MugenMicko/voron/V0/5015_Toolhead/images/back.png

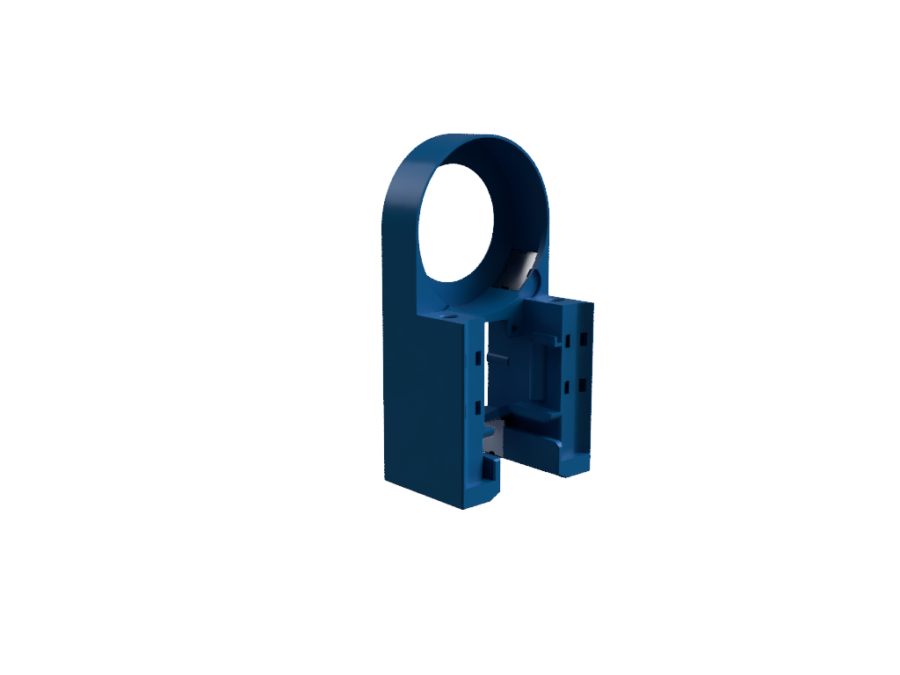
V0/5015_Toolhead/images/back.png
