MugenMicko/voron/V0/5015_Toolhead/images/front.png

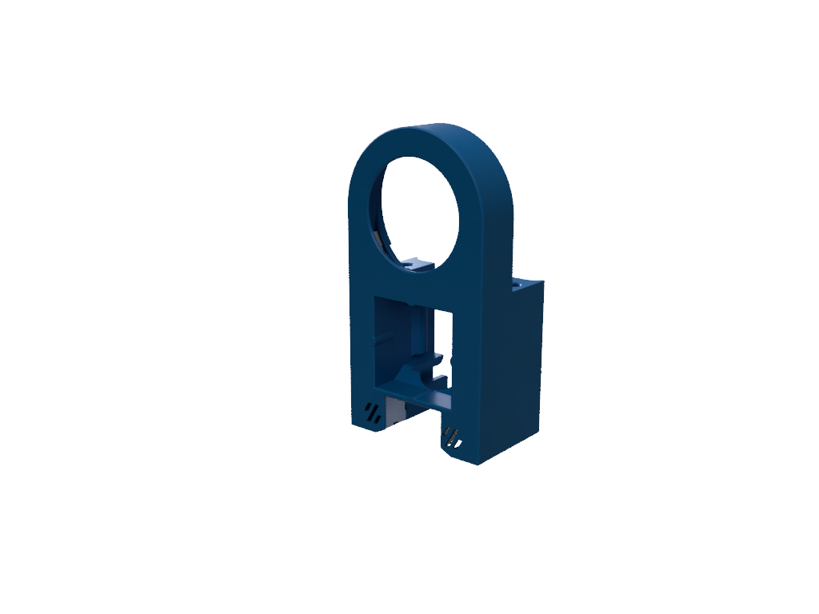
V0/5015_Toolhead/images/front.png
