MugenMicko/voron/V0/5015_Toolhead/images/ledsupports.png

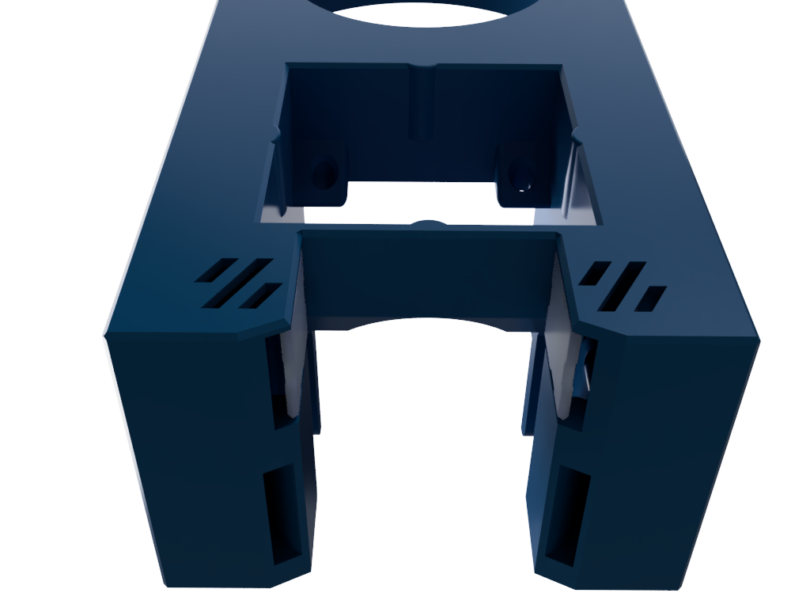
V0/5015_Toolhead/images/ledsupports.png
