MugenMicko/voron/V0/5015_Toolhead/images/PocketWatch2.jpg

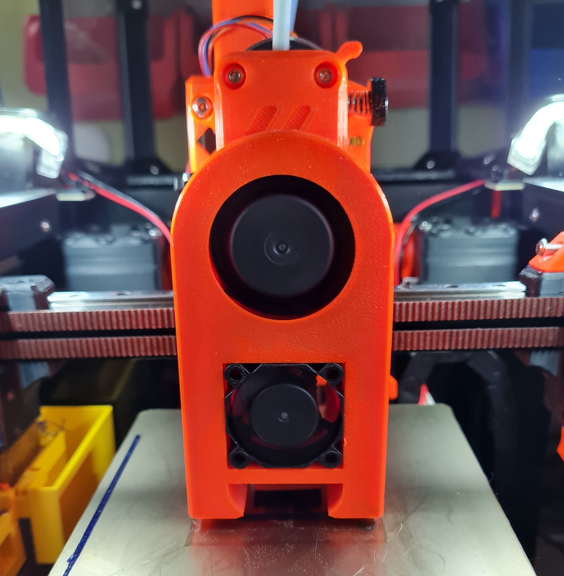
V0/5015_Toolhead/images/PocketWatch2.jpg
