MugenMicko/voron/V0/Dragon_Burner/images/airflow_db2.png

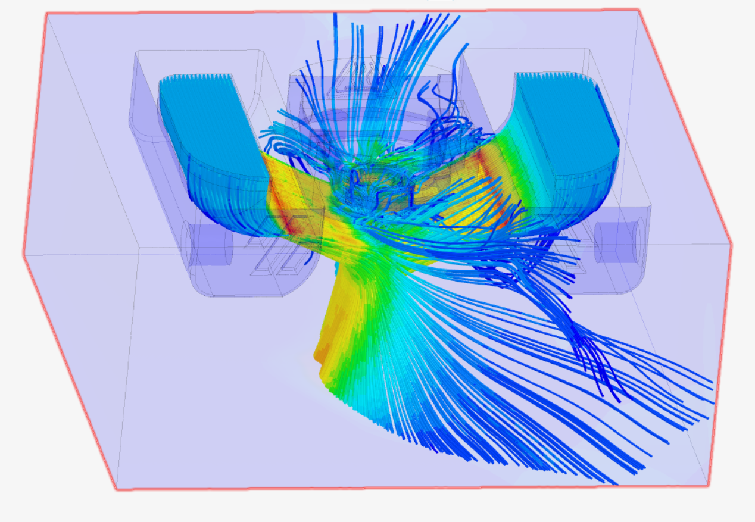
V0/Dragon_Burner/images/airflow_db2.png
