MugenMicko/voron/V0/Dragon_Burner/images/airflow_db.png

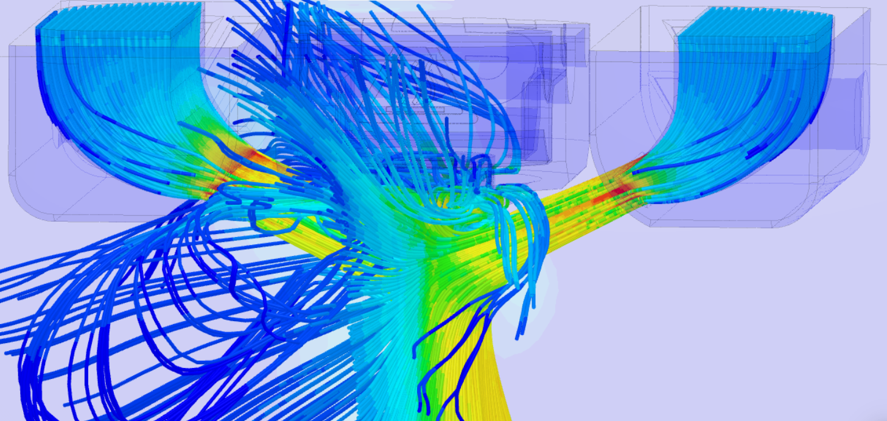
V0/Dragon_Burner/images/airflow_db.png
