MugenMicko/voron/V0/Dragon_Burner/images/airflowdb3.png

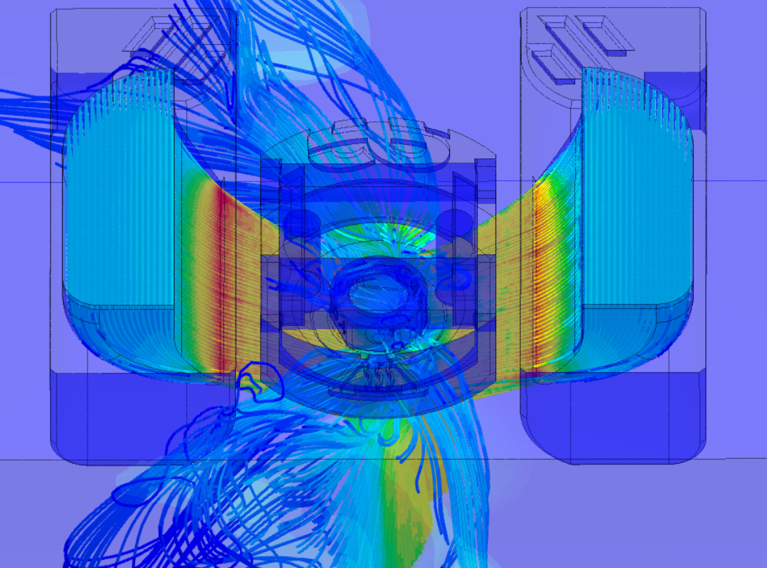
V0/Dragon_Burner/images/airflowdb3.png
