MugenMicko/voron/V0/NozzleWiper/images/mounted.jpg

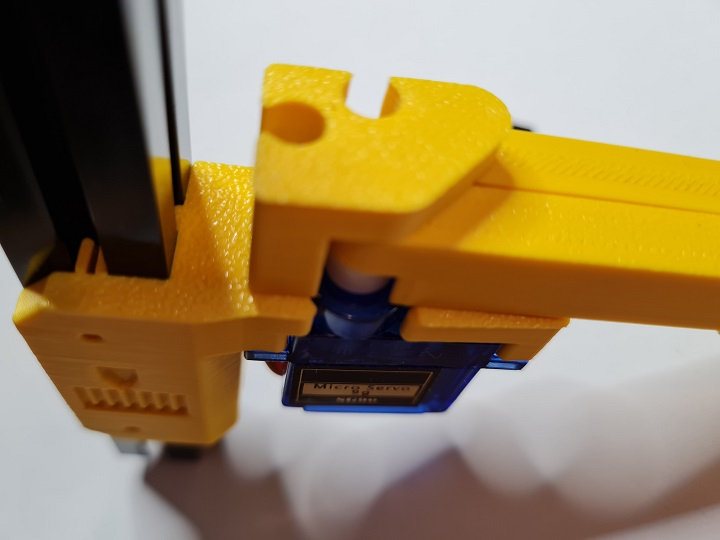
V0/NozzleWiper/images/mounted.jpg
