MugenMicko/voron/V0/NozzleWiper/images/wireplacement.jpg

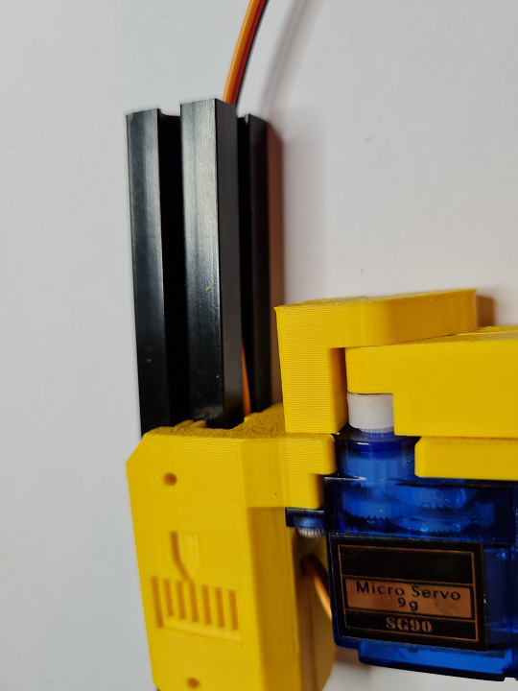
V0/NozzleWiper/images/wireplacement.jpg
