MugenMicko/voron/V0/Rapid_Burner/images/hf.png

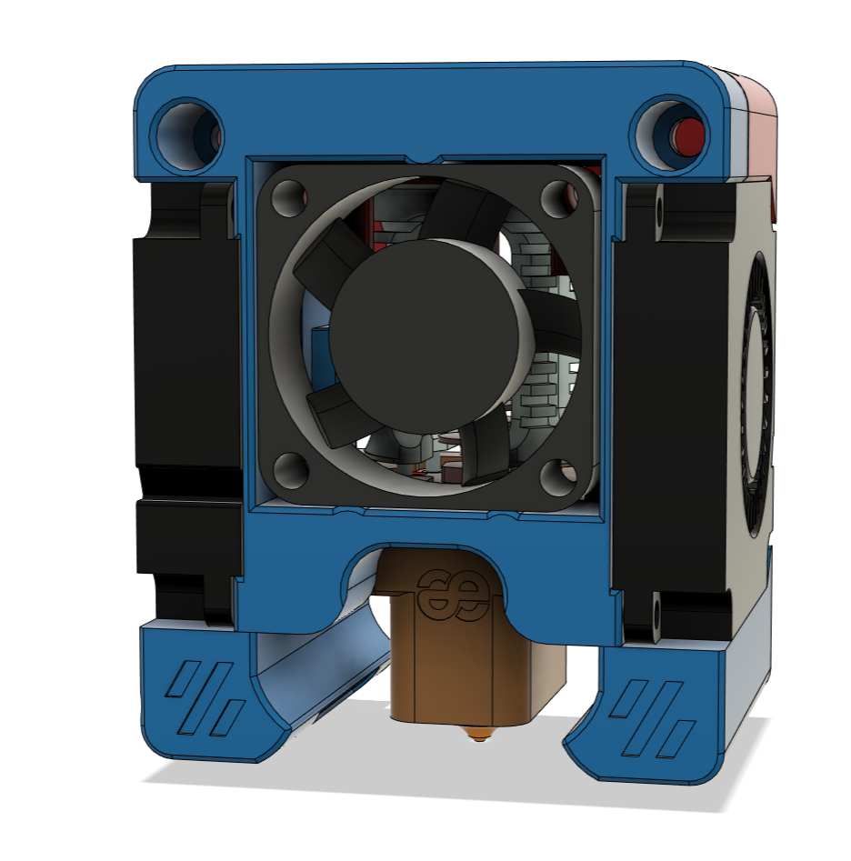
V0/Rapid_Burner/images/hf.png
