MugenMicko/voron/V0/TipTophat/images/toppanel.jpg

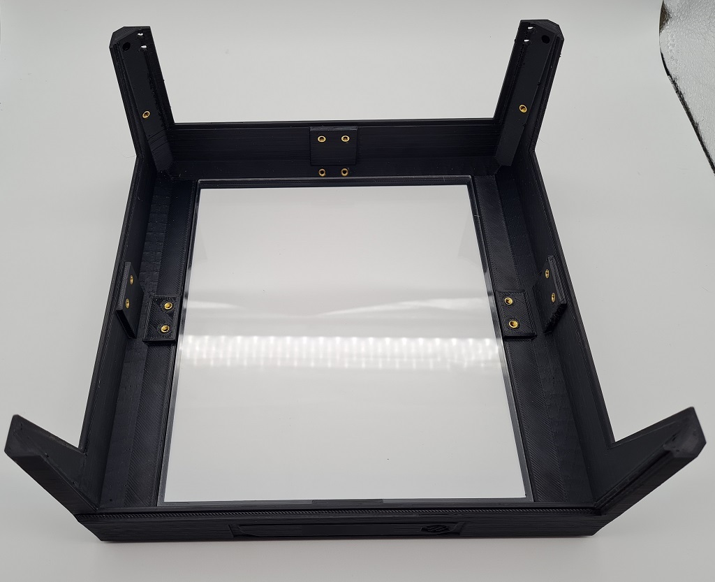
V0/TipTophat/images/toppanel.jpg
