MugenMicko/voron/general/RoundAbout/STLs/Latch.stl

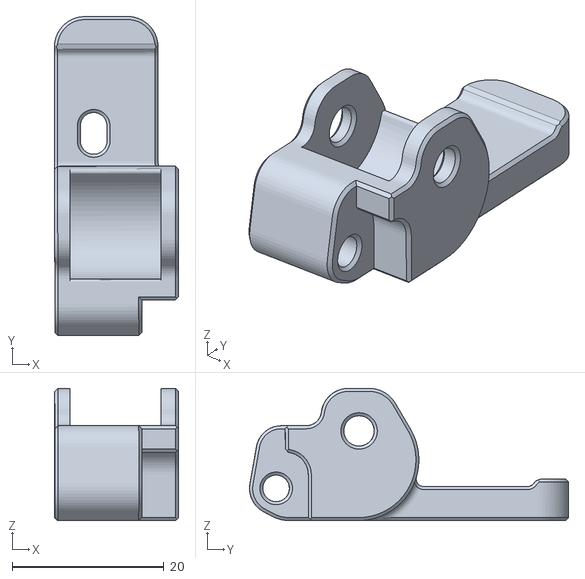
[picture p148: CAD file, 2022-09-11]
general/RoundAbout/STLs/Latch.stl
16.4 x 42.0 x 17.4
