MugenMicko/voron/general/RunoutUnklicky/STLs/Roller.stl

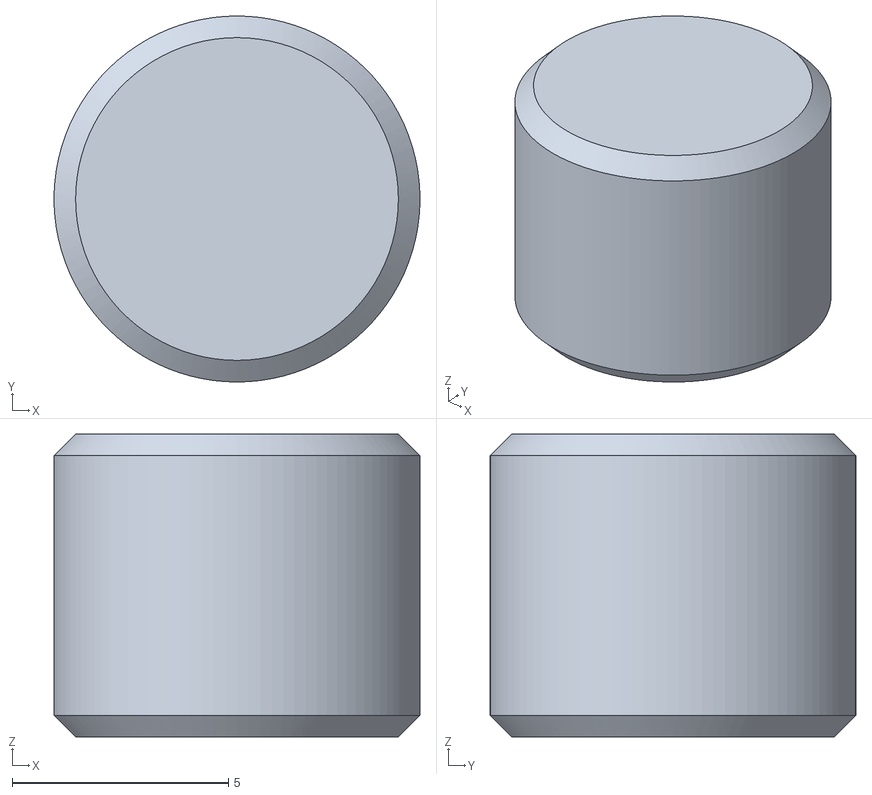
[picture p149: CAD file, 2022-07-18]
general/RunoutUnklicky/STLs/Roller.stl
8.46 x 8.46 x 7.00
