MugenMicko/voron/V0/5015_Toolhead/STLs/Bowden_Mount.stl

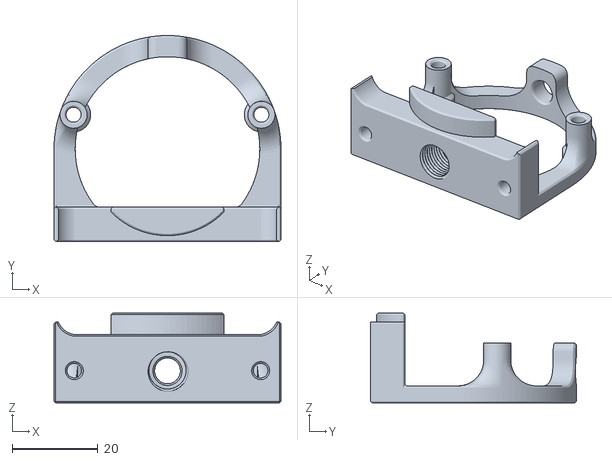
[picture p150: CAD file, 2022-09-22]
V0/5015_Toolhead/STLs/Bowden_Mount.stl
53.0 x 48.1 x 21.0
