MugenMicko/voron/V0/Dragon_Burner/STLs/Cowl_SlideSwipe.stl

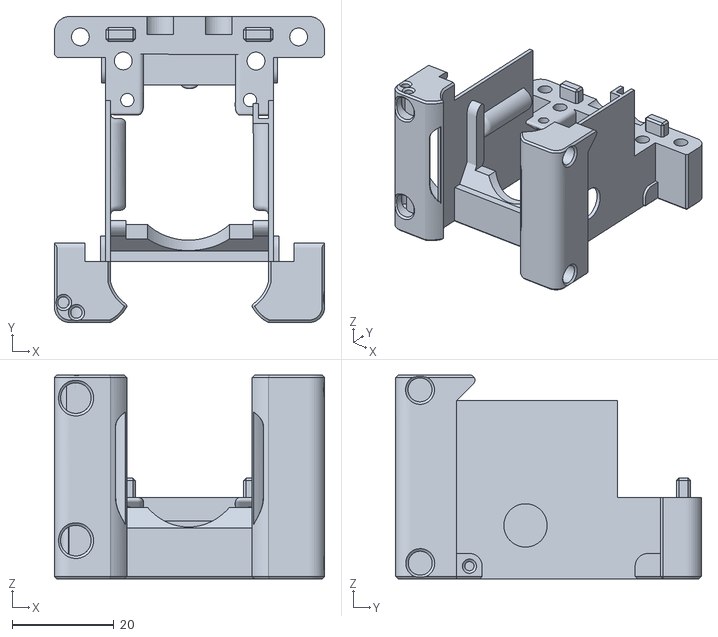
[picture p151: CAD file, 2022-09-30]
V0/Dragon_Burner/STLs/Cowl_SlideSwipe.stl
53.0 x 60.0 x 40.0
