MugenMicko/voron/V0/Dragon_Burner/STLs/Orbiter2/Dragon_Mount.stl

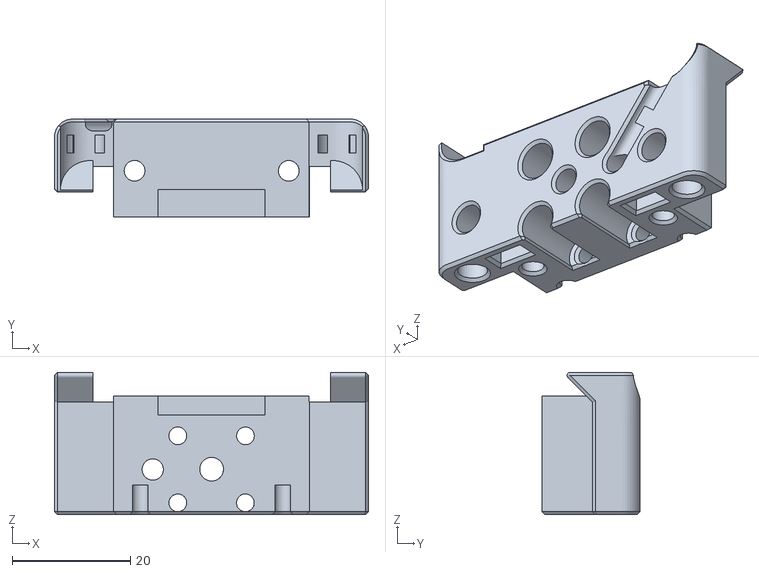
[picture p152: CAD file, 2022-08-28]
V0/Dragon_Burner/STLs/Orbiter2/Dragon_Mount.stl
53.0 x 16.5 x 24.0
