MugenMicko/voron/V0/NozzleWiper/STLs/Bucket.stl

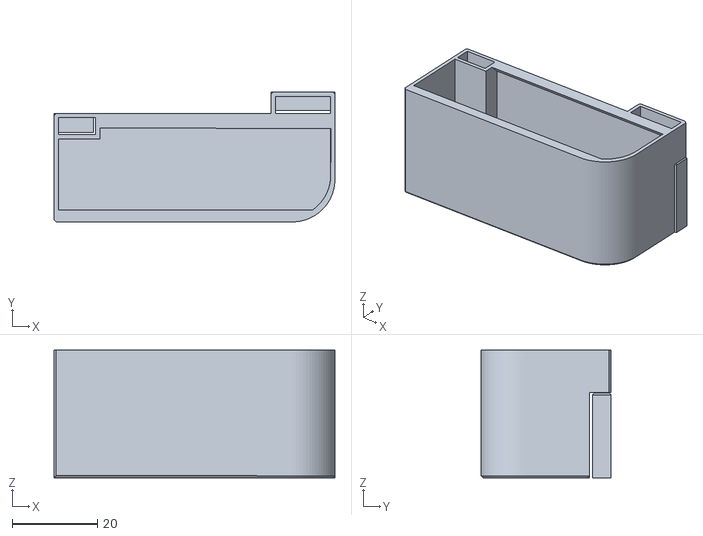
[picture p153: CAD file, 2022-09-01]
V0/NozzleWiper/STLs/Bucket.stl
66.0 x 30.5 x 30.0
