MugenMicko/voron/V0/Rapid_Burner/STLs/HF/Cowl_SlideSwipe.stl

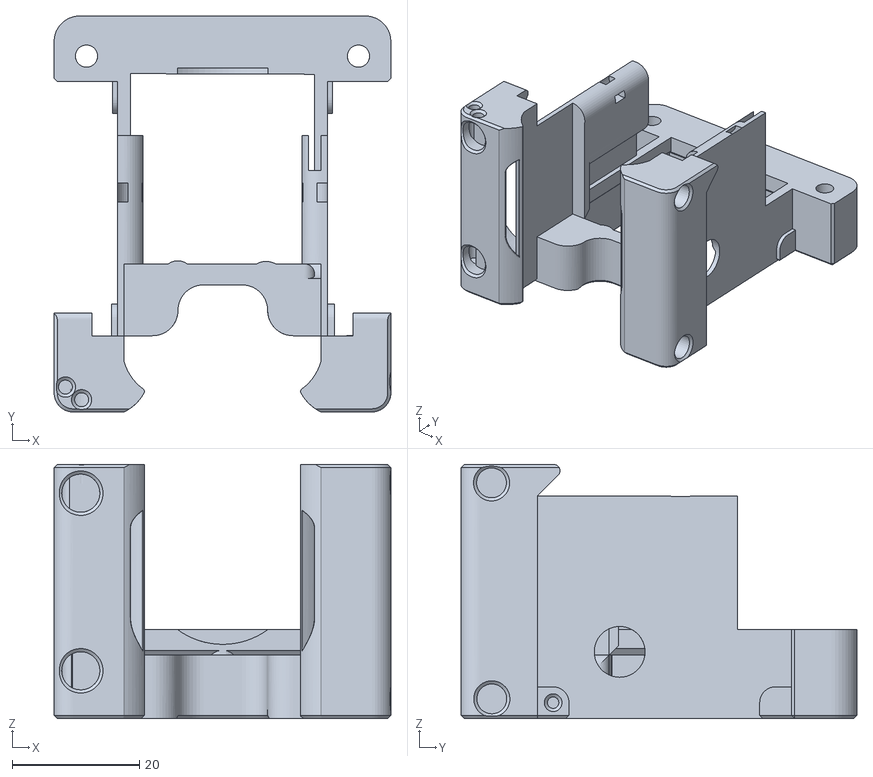
[picture p154: CAD file, 2022-09-06]
V0/Rapid_Burner/STLs/HF/Cowl_SlideSwipe.stl
53.0 x 62.3 x 40.0
