MugenMicko/voron/V0/Rapid_Burner/STLs/ZeroClick_Mount.stl

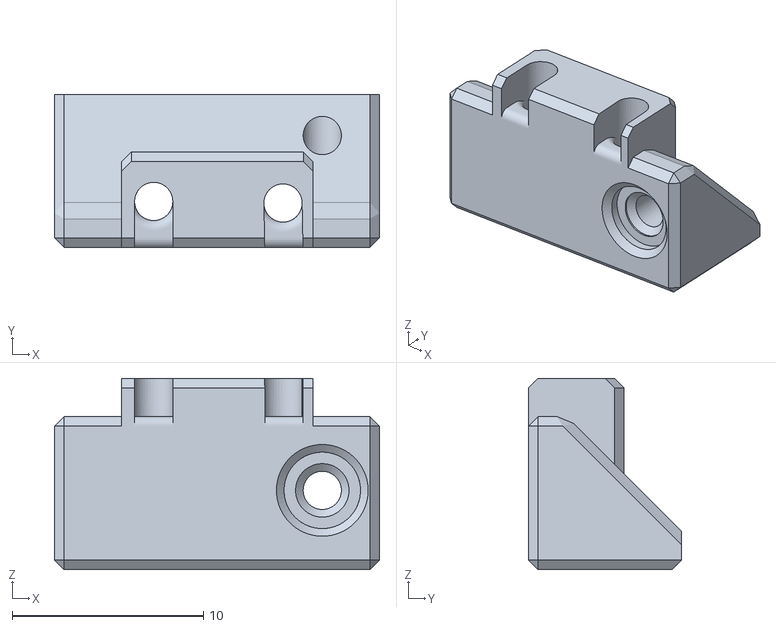
[picture p155: CAD file, 2022-09-21]
V0/Rapid_Burner/STLs/ZeroClick_Mount.stl
17.0 x 8.00 x 10.0
