MugenMicko/voron/V0/TipTophat/STLs/Peg_2_x2.stl

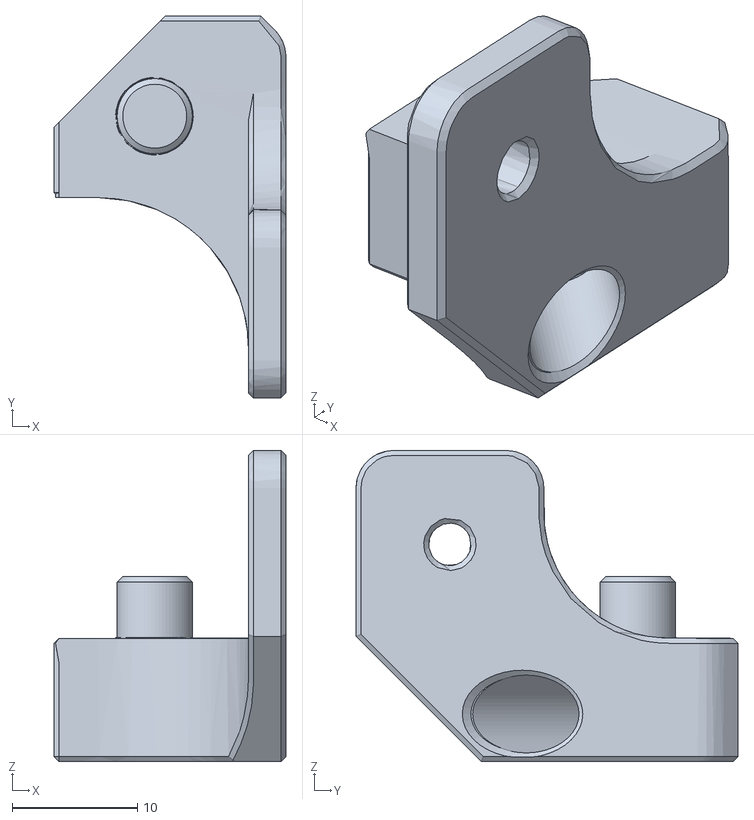
[picture p156: CAD file, 2022-07-24]
V0/TipTophat/STLs/Peg_2_x2.stl
18.5 x 30.5 x 24.8
