MugenMicko/voron/general/MiniMouse/STLs/MiniMouse_Guidler.stl

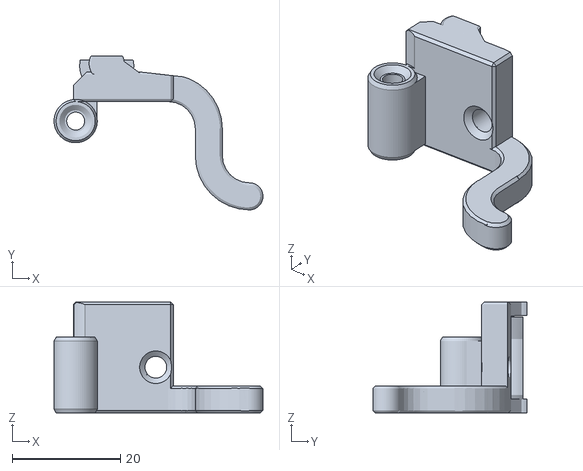
[picture p157: CAD file, 2022-06-26]
general/MiniMouse/STLs/MiniMouse_Guidler.stl
38.6 x 28.4 x 20.5
