MugenMicko/voron/general/RoundAbout/STLs/Support_Ring.stl

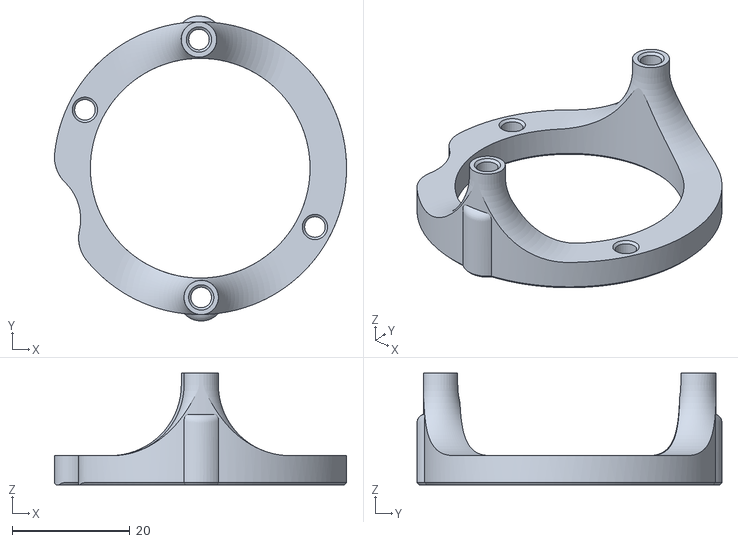
[picture p158: CAD file, 2022-09-11]
general/RoundAbout/STLs/Support_Ring.stl
49.6 x 51.8 x 19.0
