MugenMicko/voron/general/RoundHouse/STLs/Guidler.stl

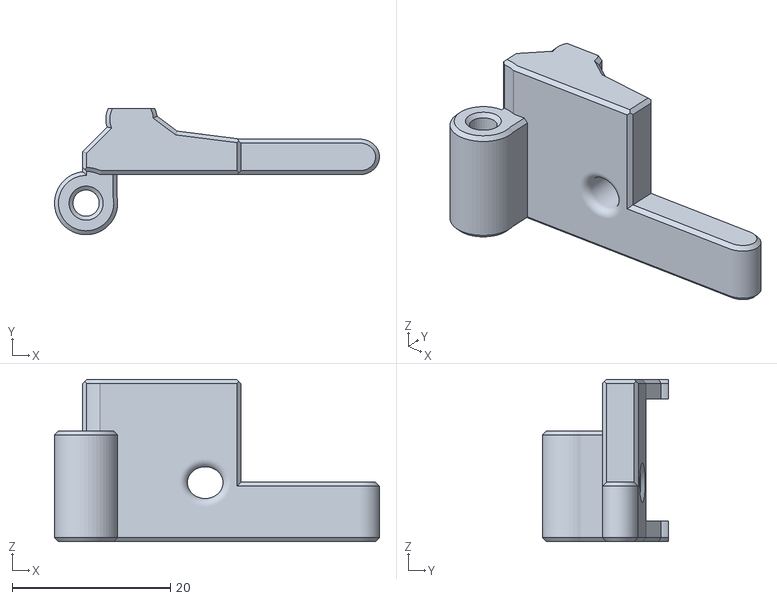
[picture p159: CAD file, 2022-08-05]
general/RoundHouse/STLs/Guidler.stl
41.1 x 16.0 x 20.5
