MugenMicko/voron/general/RunoutUnklicky/STLs/Top_2020.stl

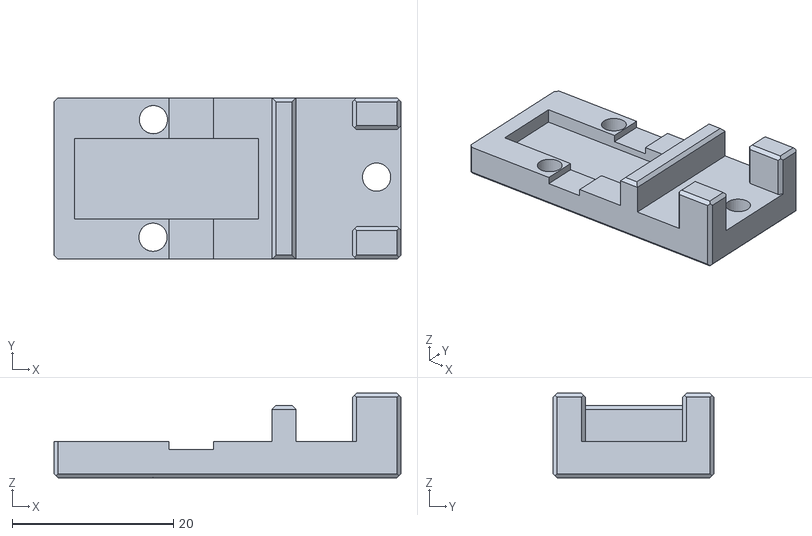
[picture p160: CAD file, 2022-07-15]
general/RunoutUnklicky/STLs/Top_2020.stl
43.0 x 20.0 x 10.5
