MugenMicko/voron/V0/5015_Toolhead/STLs/Fan_Cover.stl

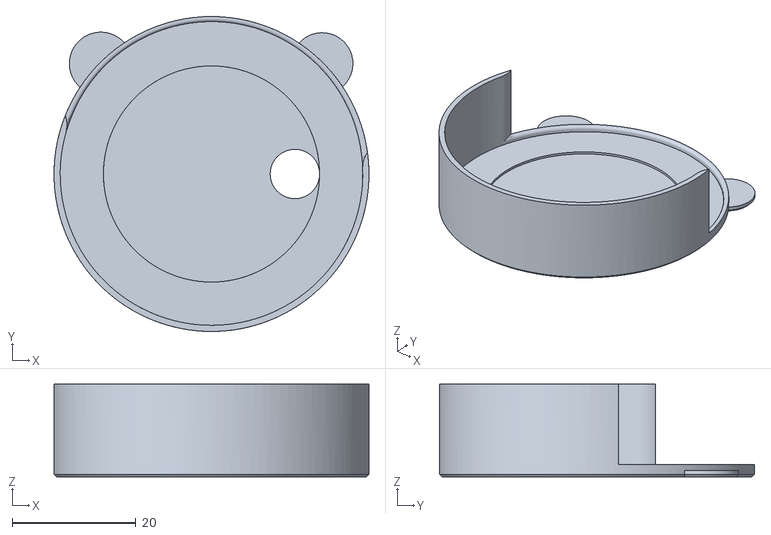
[picture p161: CAD file, 2022-09-12]
V0/5015_Toolhead/STLs/Fan_Cover.stl
51.0 x 51.0 x 15.0
