MugenMicko/voron/V0/Dragon_Burner/STLs/Orbiter1.5/Orbiter1.5_Mount.stl

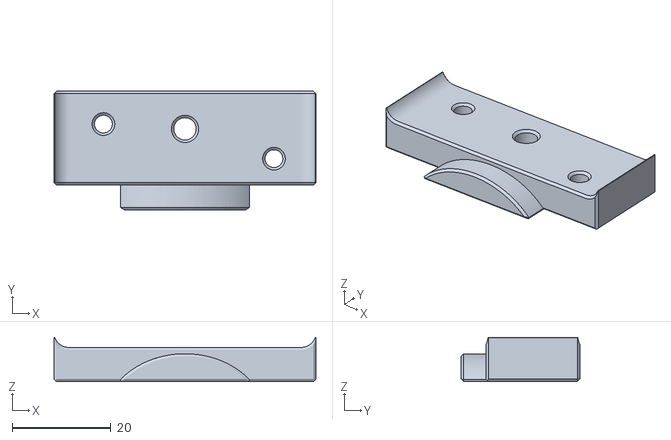
[picture p162: CAD file, 2022-08-29]
V0/Dragon_Burner/STLs/Orbiter1.5/Orbiter1.5_Mount.stl
53.0 x 24.1 x 8.90
