MugenMicko/voron/V0/NozzleWiper/STLs/Frame_Mount.stl

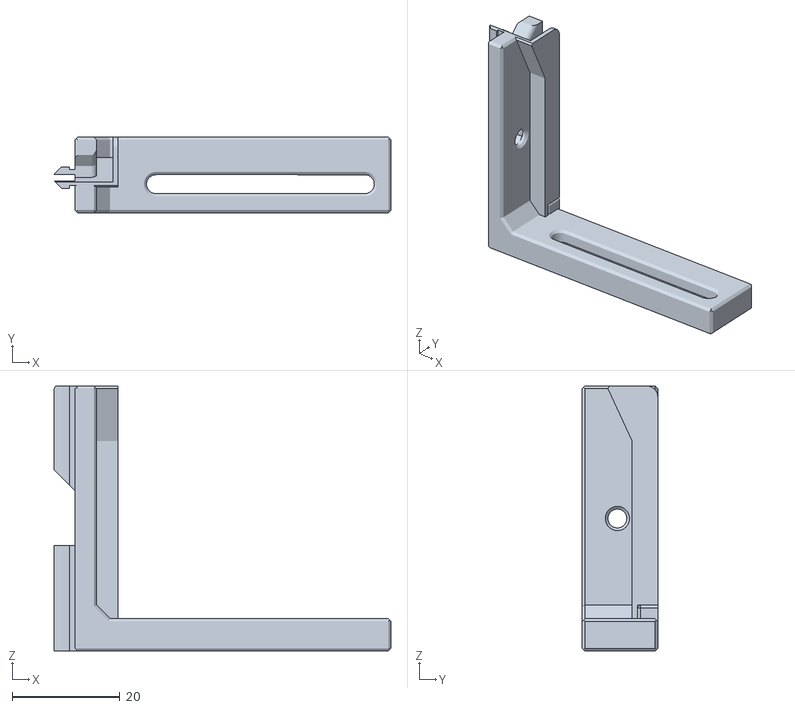
[picture p164: CAD file, 2022-08-21]
V0/NozzleWiper/STLs/Frame_Mount.stl
62.4 x 14.0 x 49.1
