MugenMicko/voron/V0/Rapid_Burner/STLs/Cowl_ZeroClick.stl

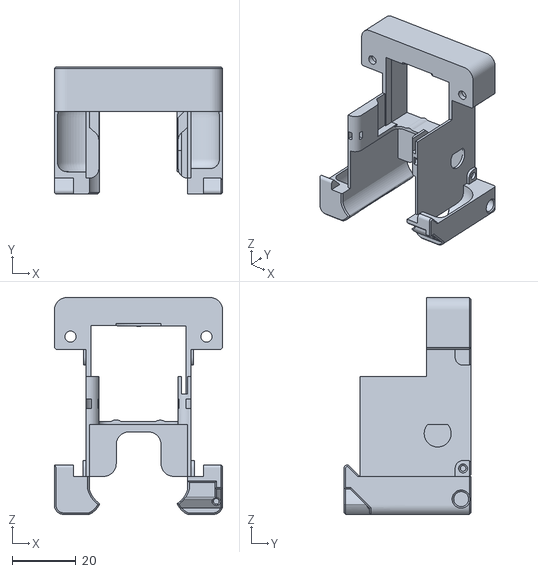
[picture p165: CAD file, 2022-09-21]
V0/Rapid_Burner/STLs/Cowl_ZeroClick.stl
53.0 x 40.0 x 68.3
