MugenMicko/voron/V0/TipTophat/STLs/Body_Q3.stl

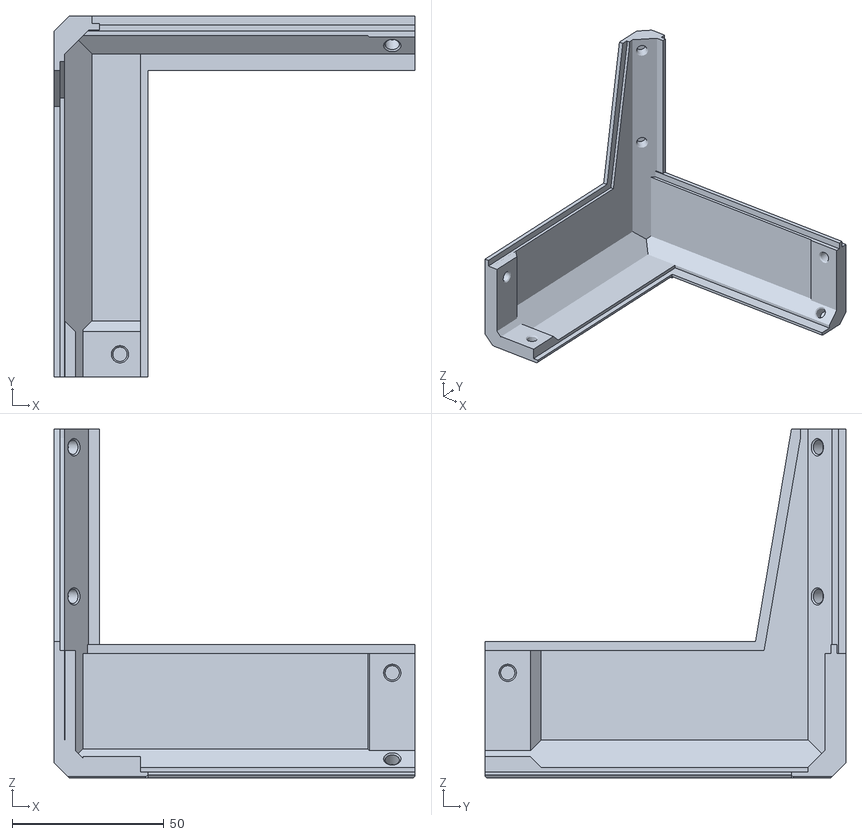
[picture p166: CAD file, 2022-07-12]
V0/TipTophat/STLs/Body_Q3.stl
119.0 x 119.0 x 115.0
