MugenMicko/voron/general/RoundAbout/STLs/Back.stl

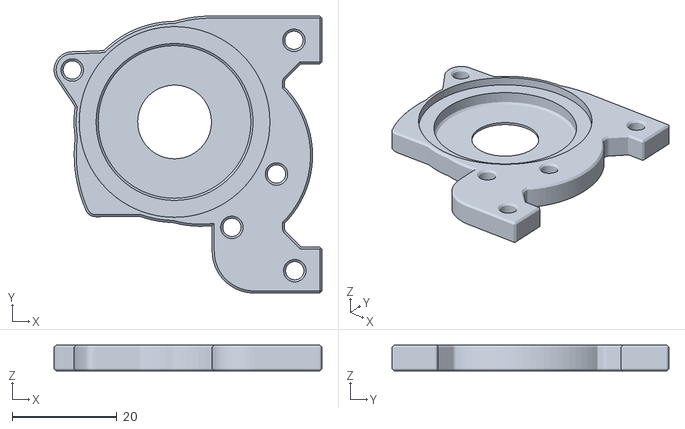
[picture p167: CAD file, 2022-09-11]
general/RoundAbout/STLs/Back.stl
51.2 x 53.0 x 4.95
