MugenMicko/voron/general/RunoutUnklicky/STLs/Top.stl

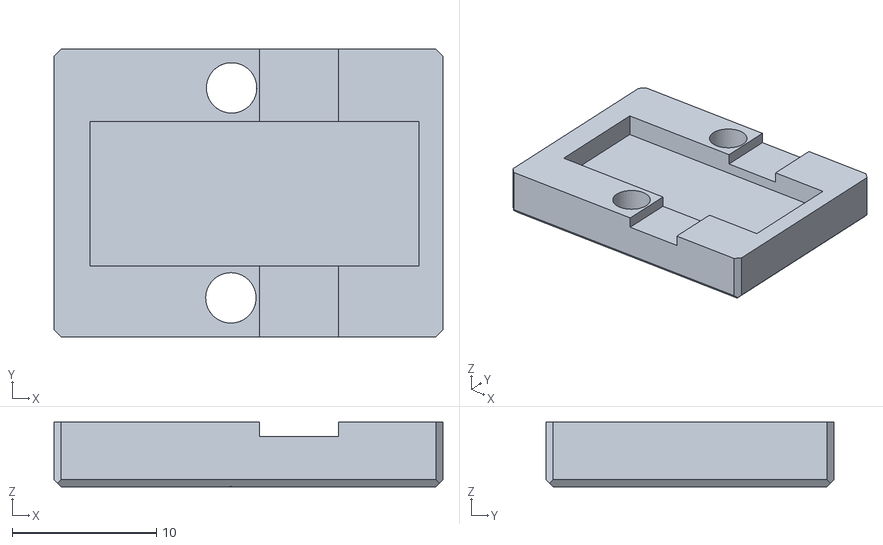
[picture p168: CAD file, 2022-07-15]
general/RunoutUnklicky/STLs/Top.stl
27.0 x 20.0 x 4.50
