MugenMicko/voron/V0/5015_Toolhead/STLs/Extruder_Mount.stl

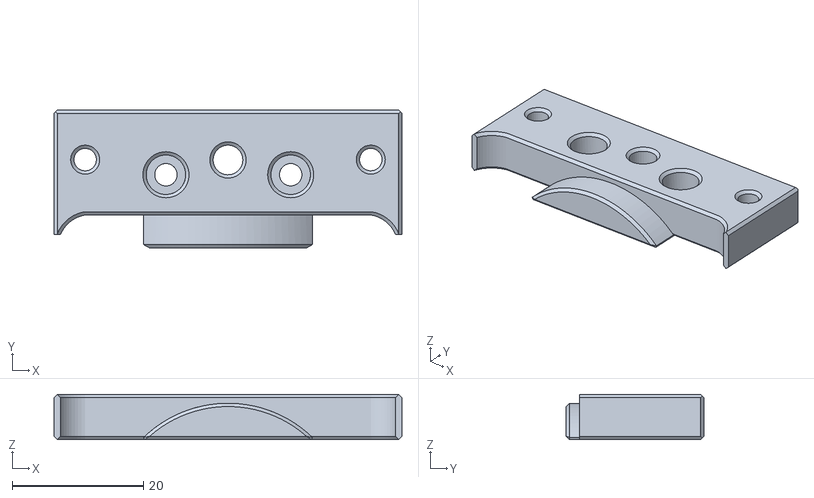
[picture p169: CAD file, 2022-08-30]
V0/5015_Toolhead/STLs/Extruder_Mount.stl
53.0 x 21.0 x 6.90
