MugenMicko/voron/V0/Dragon_Burner/STLs/Orbiter2/RapidoHF_Mount.stl

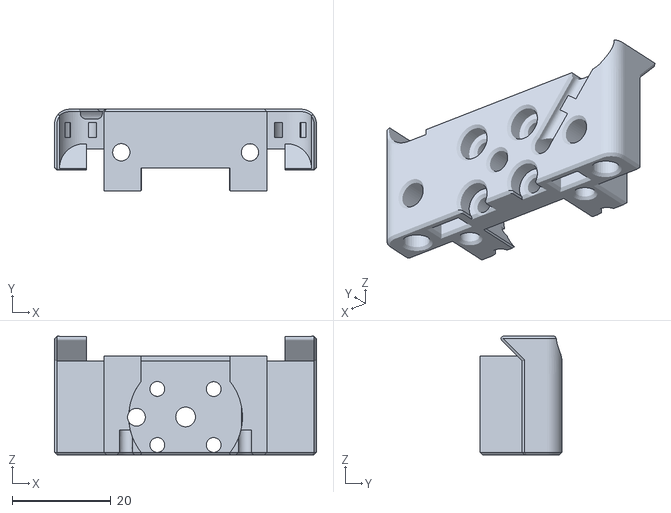
[picture p171: CAD file, 2022-08-28]
V0/Dragon_Burner/STLs/Orbiter2/RapidoHF_Mount.stl
53.0 x 16.5 x 24.0
