MugenMicko/voron/V0/NozzleWiper/STLs/Servo_Joint.stl

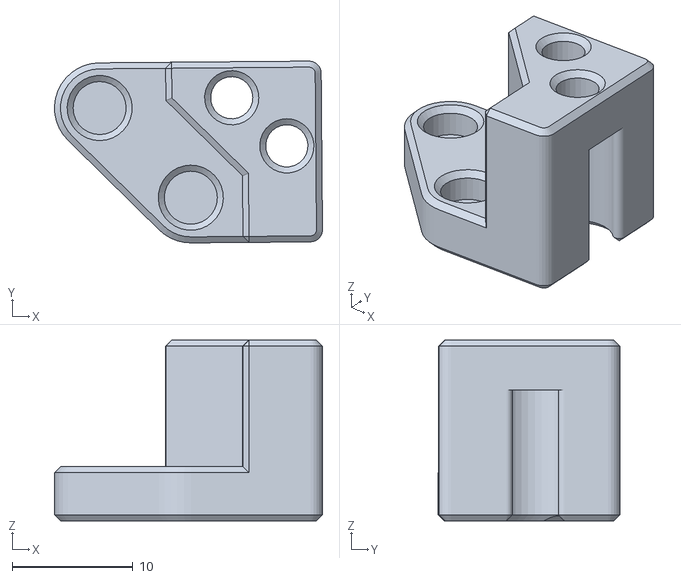
[picture p172: CAD file, 2022-08-21]
V0/NozzleWiper/STLs/Servo_Joint.stl
22.2 x 15.1 x 15.0
