MugenMicko/voron/V0/TipTophat/STLs/Body_Q4.stl

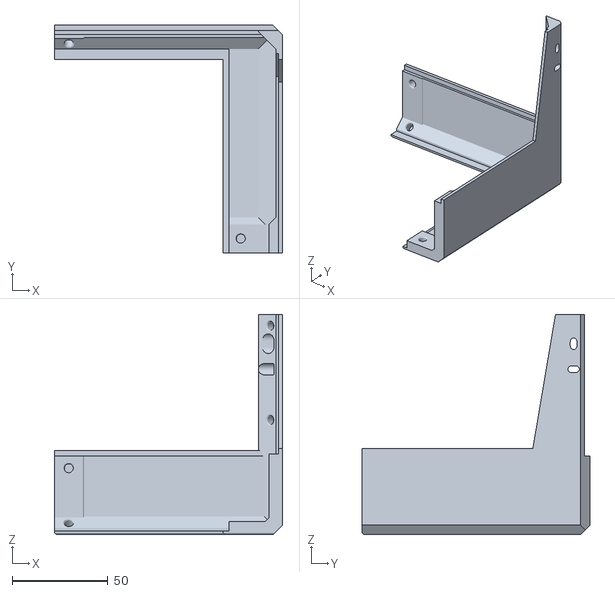
[picture p173: CAD file, 2022-07-12]
V0/TipTophat/STLs/Body_Q4.stl
119.0 x 119.0 x 115.0
