MugenMicko/voron/general/RunoutUnklicky/STLs/Top_1515.stl

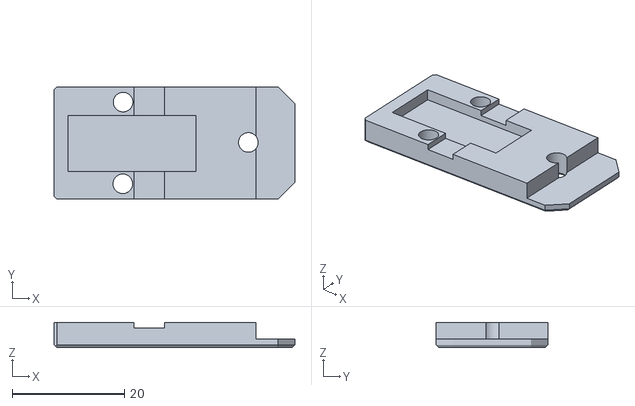
[picture p174: CAD file, 2022-07-15]
general/RunoutUnklicky/STLs/Top_1515.stl
43.0 x 20.0 x 4.50
