MugenMicko/voron/V0/5015_Toolhead/STLs/NF_Crazy_Mount.stl

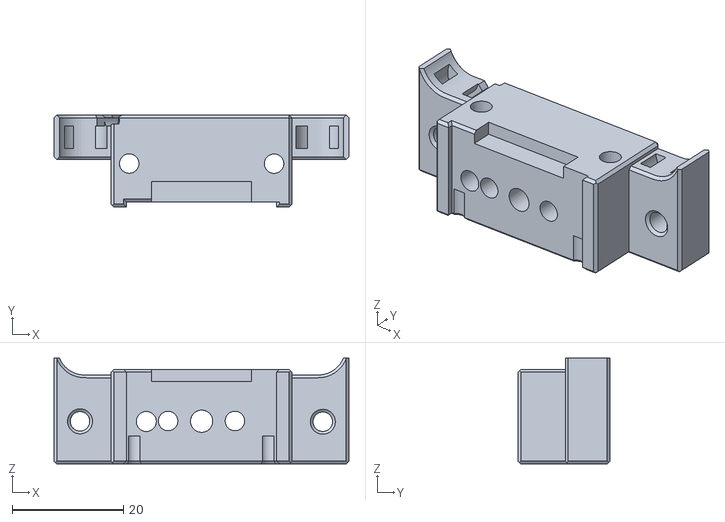
[picture p175: CAD file, 2022-08-30]
V0/5015_Toolhead/STLs/NF_Crazy_Mount.stl
53.0 x 16.5 x 19.0
