MugenMicko/voron/V0/Dragon_Burner/STLs/Orbiter1.5/RevoVoron_Mount.stl

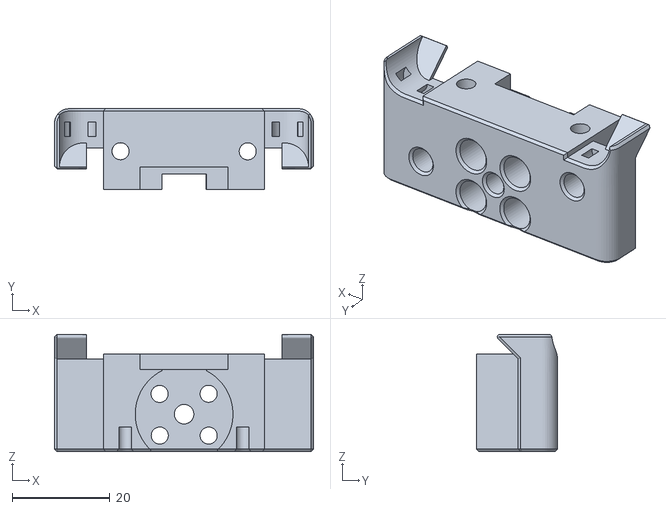
[picture p176: CAD file, 2022-08-29]
V0/Dragon_Burner/STLs/Orbiter1.5/RevoVoron_Mount.stl
53.0 x 16.5 x 24.0
