MugenMicko/voron/V0/NozzleWiper/STLs/Servo_Mount.stl

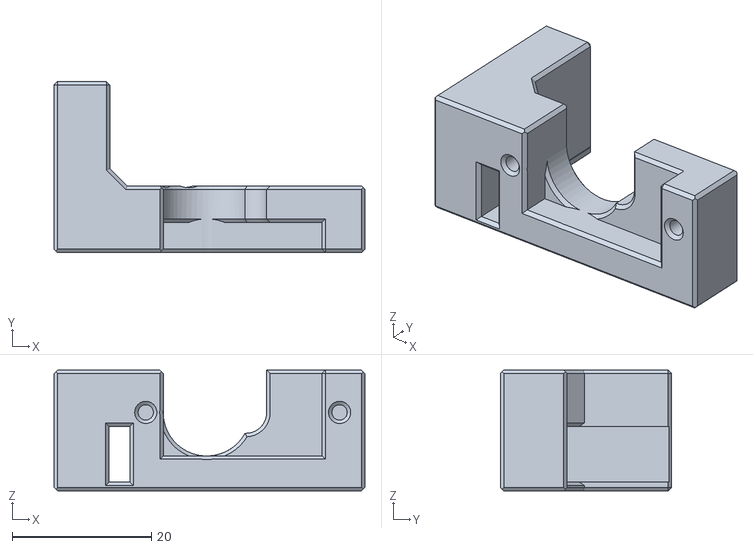
[picture p177: CAD file, 2022-08-21]
V0/NozzleWiper/STLs/Servo_Mount.stl
44.6 x 24.6 x 17.4
