MugenMicko/voron/V0/Rapid_Burner/STLs/Orbiter1.5_Mount.stl

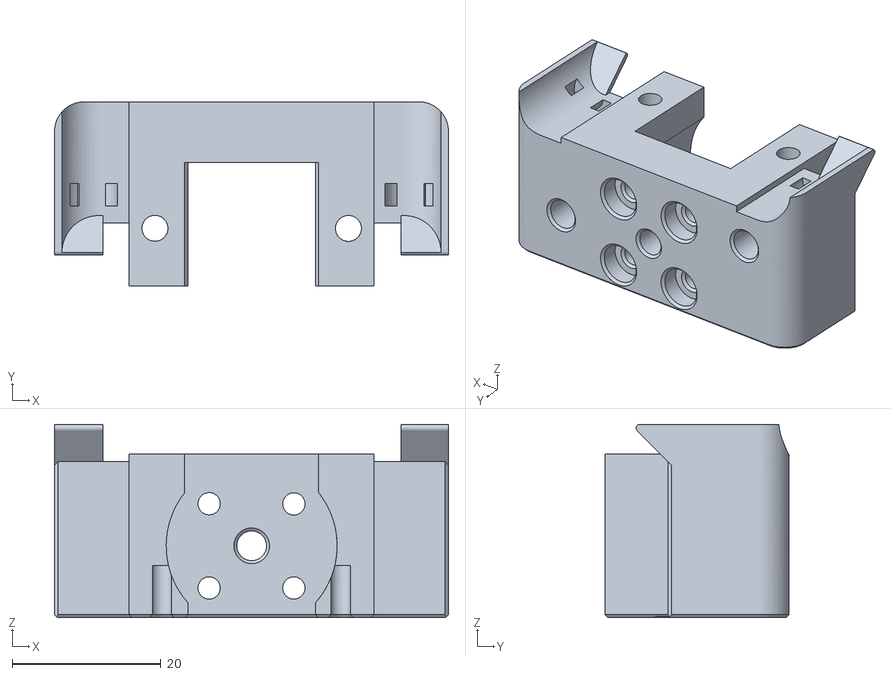
[picture p178: CAD file, 2022-09-04]
V0/Rapid_Burner/STLs/Orbiter1.5_Mount.stl
53.0 x 24.8 x 26.0
