MugenMicko/voron/V0/TipTophat/STLs/Body_Q2.stl

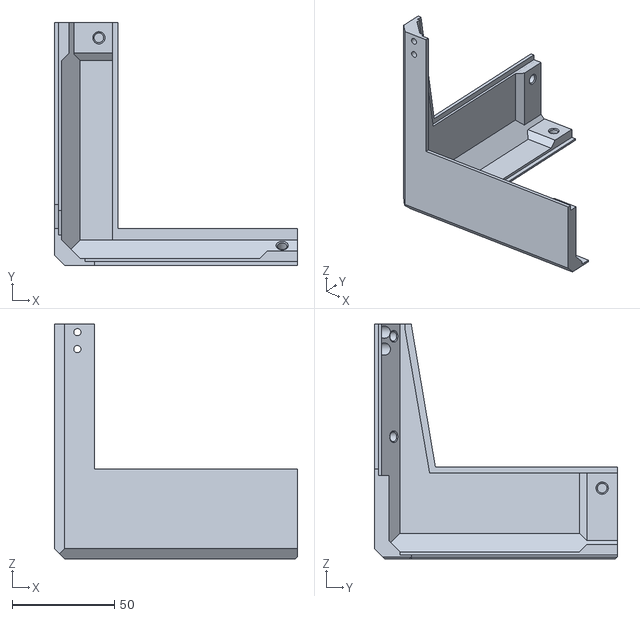
[picture p179: CAD file, 2022-07-03]
V0/TipTophat/STLs/Body_Q2.stl
119.0 x 119.0 x 115.0
