MugenMicko/voron/general/RunoutUnklicky/STLs/Base_PC4-M6.stl

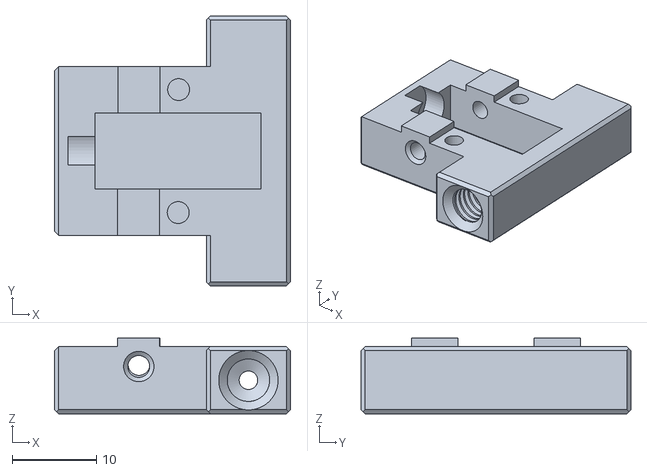
[picture p180: CAD file, 2022-07-15]
general/RunoutUnklicky/STLs/Base_PC4-M6.stl
28.0 x 32.0 x 9.00
