MugenMicko/voron/V0/5015_Toolhead/STLs/[c]_LED_Cover_Left.stl

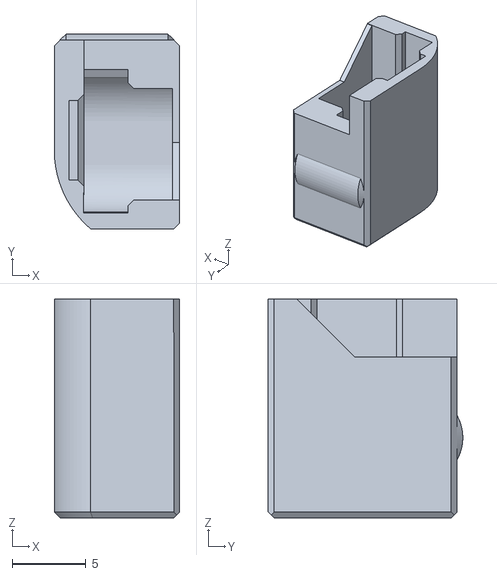
[picture p181: CAD file, 2022-08-30]
V0/5015_Toolhead/STLs/[c]_LED_Cover_Left.stl
8.50 x 13.2 x 14.8
