MugenMicko/voron/V0/Dragon_Burner/STLs/Orbiter2/Orbiter2_Mount.stl

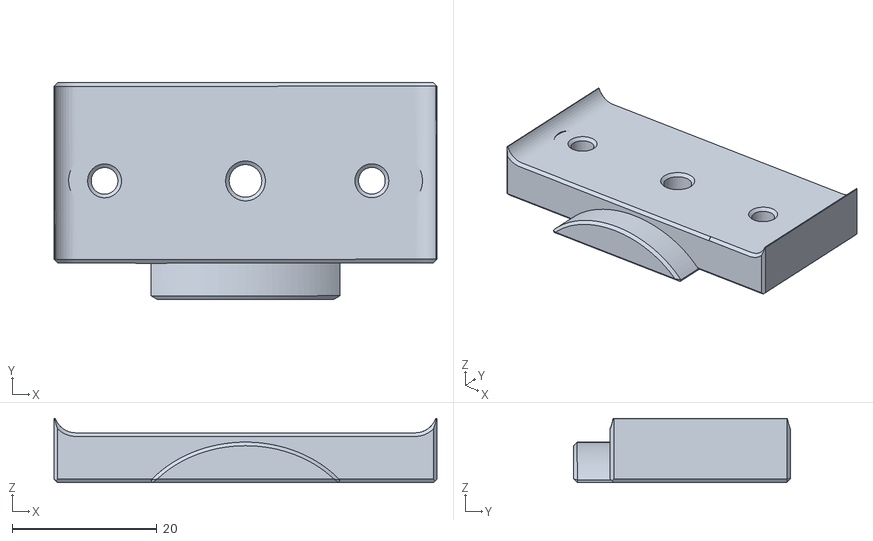
[picture p182: CAD file, 2022-08-28]
V0/Dragon_Burner/STLs/Orbiter2/Orbiter2_Mount.stl
53.0 x 30.0 x 8.91
