MugenMicko/voron/V0/NozzleWiper/STLs/Servo_Mount_MG90.stl

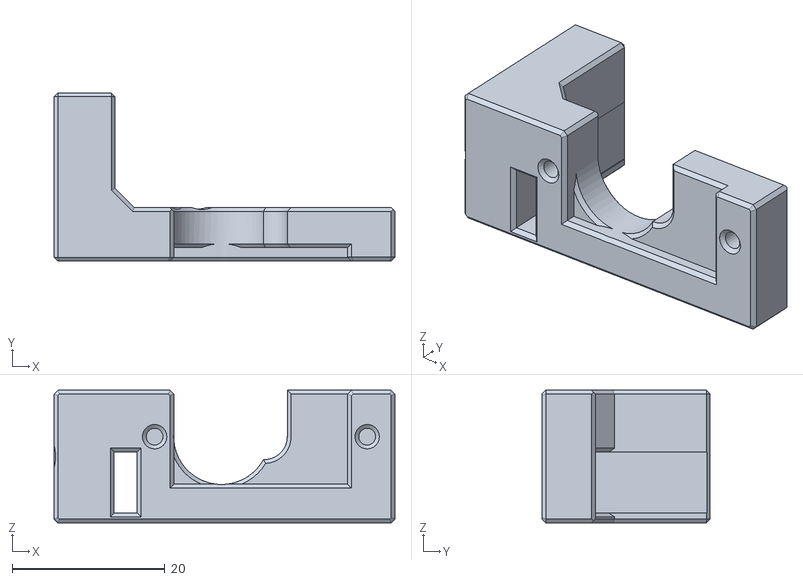
[picture p183: CAD file, 2022-08-21]
V0/NozzleWiper/STLs/Servo_Mount_MG90.stl
44.6 x 22.0 x 17.4
