MugenMicko/voron/general/RunoutUnklicky/STLs/Top_1515_NoNut.stl

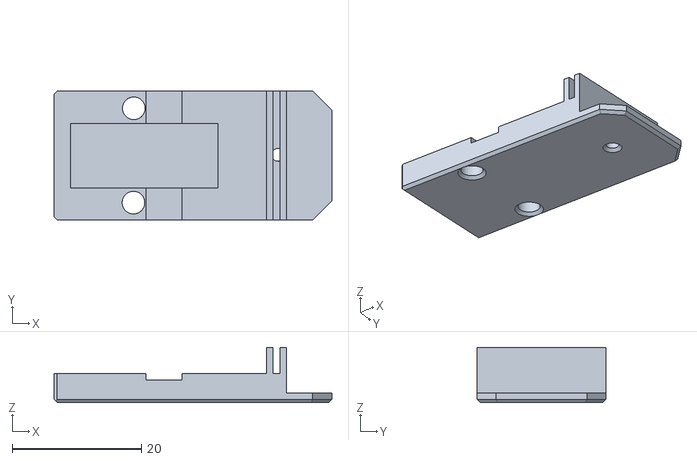
[picture p184: CAD file, 2022-07-15]
general/RunoutUnklicky/STLs/Top_1515_NoNut.stl
42.9 x 20.0 x 8.50
