MugenMicko/voron/V0/5015_Toolhead/STLs/Cowl_SlideSwipe.stl

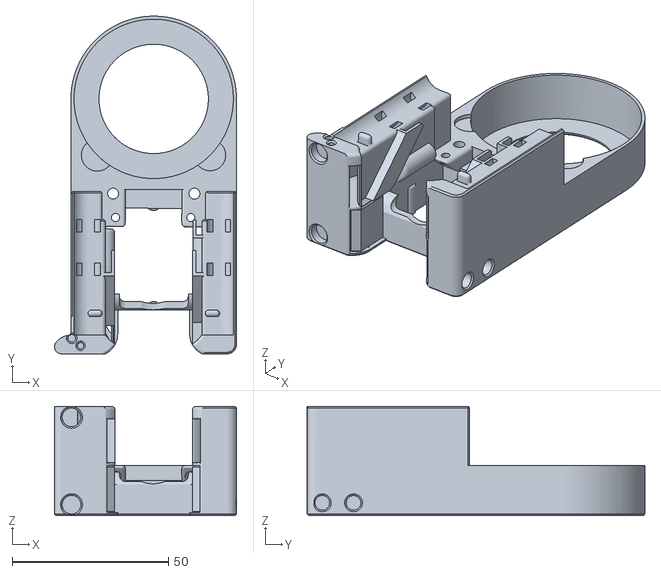
[picture p185: CAD file, 2022-08-30]
V0/5015_Toolhead/STLs/Cowl_SlideSwipe.stl
58.2 x 108.1 x 35.0
