MugenMicko/voron/V0/Dragon_Burner/STLs/ZeroClick_Mount.stl

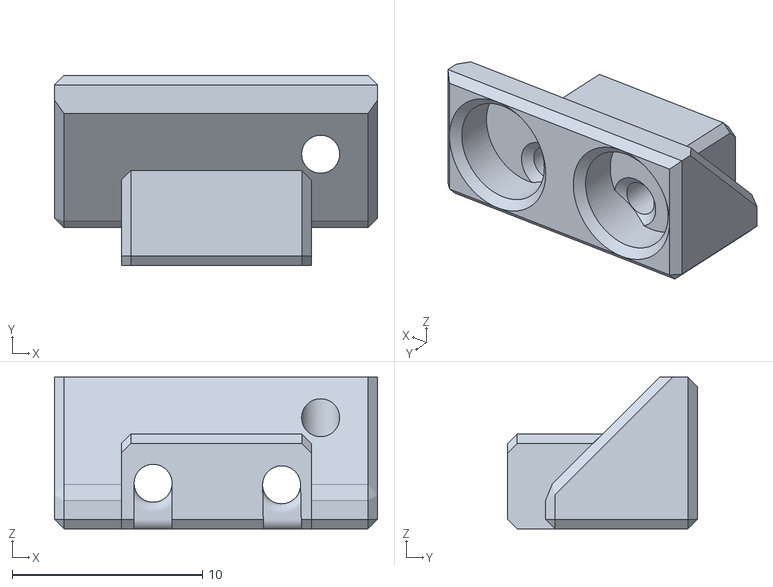
[picture p186: CAD file, 2022-09-21]
V0/Dragon_Burner/STLs/ZeroClick_Mount.stl
17.0 x 10.0 x 8.00
