MugenMicko/voron/V0/NozzleWiper/STLs/Parallel_Arm.stl

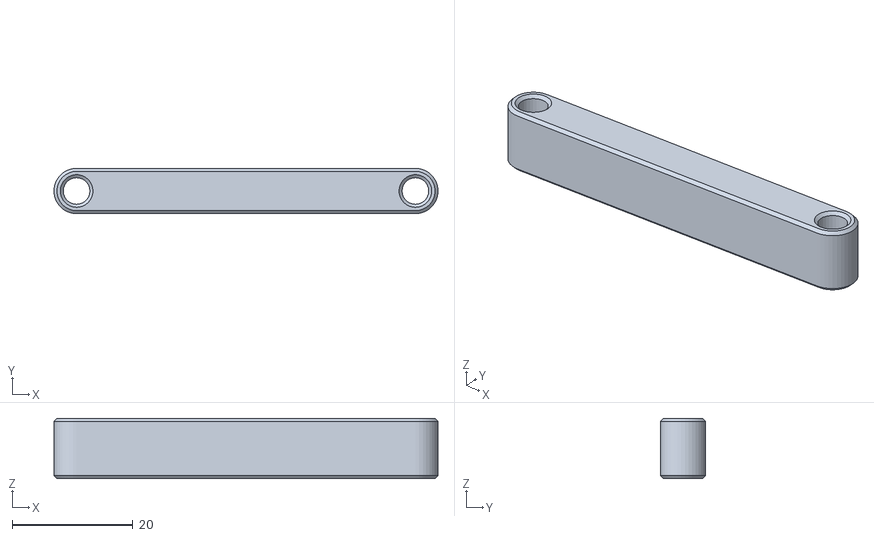
[picture p187: CAD file, 2022-08-21]
V0/NozzleWiper/STLs/Parallel_Arm.stl
63.5 x 7.50 x 10.0
