MugenMicko/voron/V0/Rapid_Burner/STLs/LGX_Lite_Mount.stl

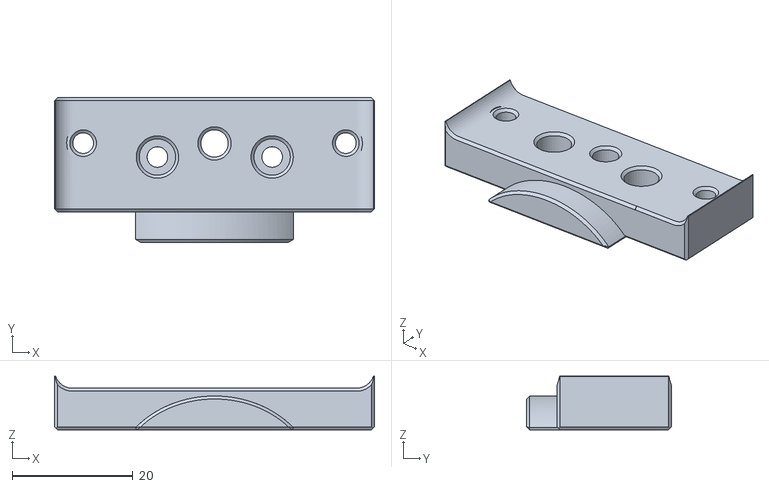
[picture p188: CAD file, 2022-09-04]
V0/Rapid_Burner/STLs/LGX_Lite_Mount.stl
53.0 x 24.0 x 8.91
