MugenMicko/voron/general/RunoutUnklicky/STLs/Base_Collet.stl

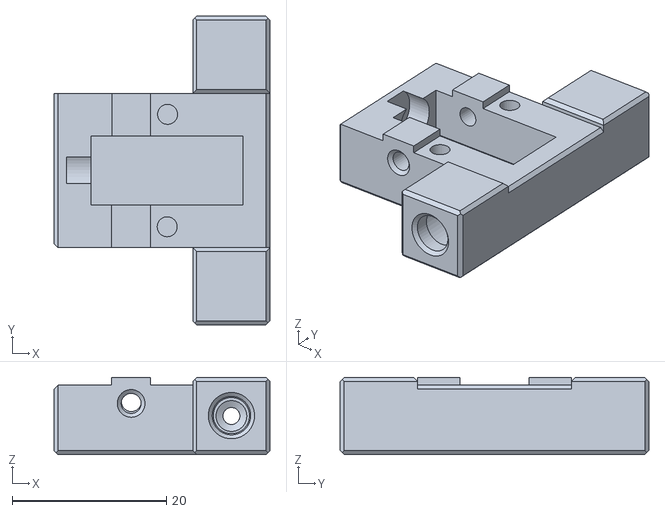
[picture p189: CAD file, 2022-07-15]
general/RunoutUnklicky/STLs/Base_Collet.stl
28.0 x 40.0 x 10.00
