MugenMicko/voron/V0/5015_Toolhead/STLs/Cowl_NoProbe.stl

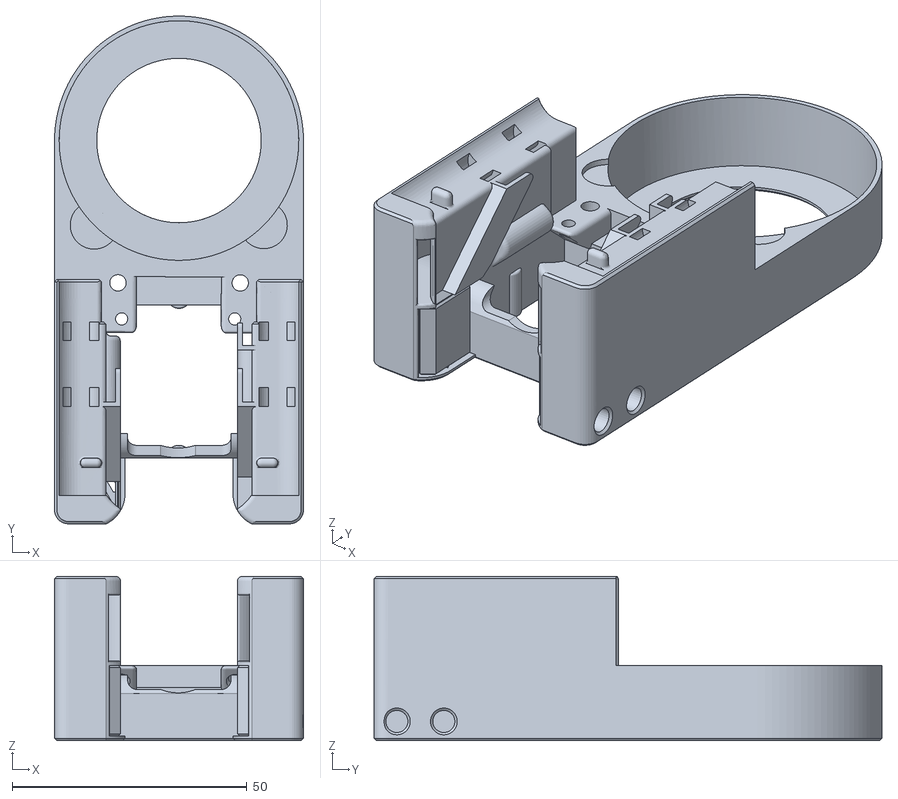
[picture p190: CAD file, 2022-08-30]
V0/5015_Toolhead/STLs/Cowl_NoProbe.stl
53.0 x 108.1 x 35.0
