MugenMicko/voron/V0/TipTophat/STLs/Door_Hinge.stl

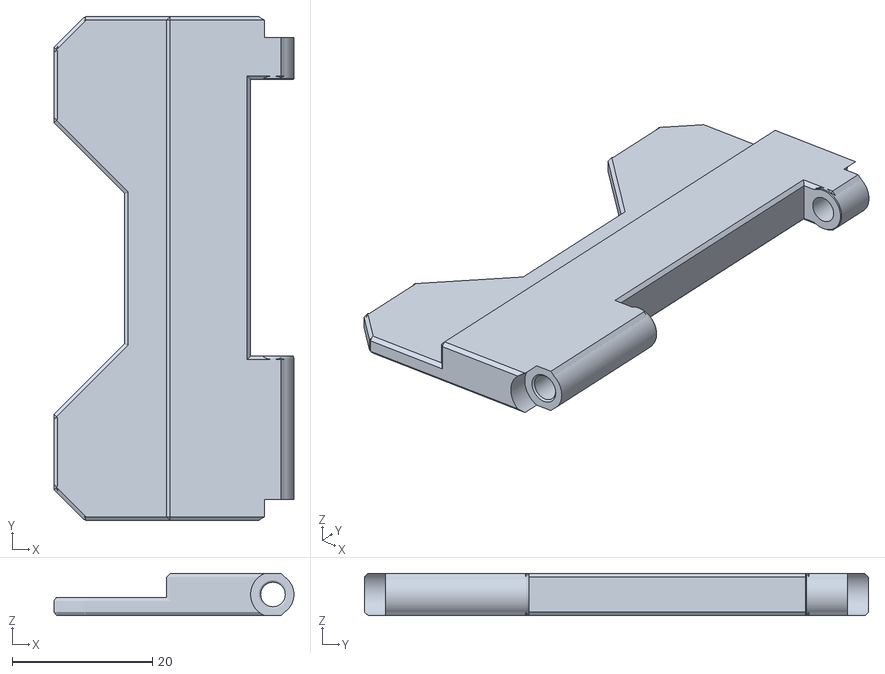
[picture p191: CAD file, 2022-06-30]
V0/TipTophat/STLs/Door_Hinge.stl
34.3 x 72.0 x 6.00
