MugenMicko/voron/general/RunoutUnklicky/STLs/Base.stl

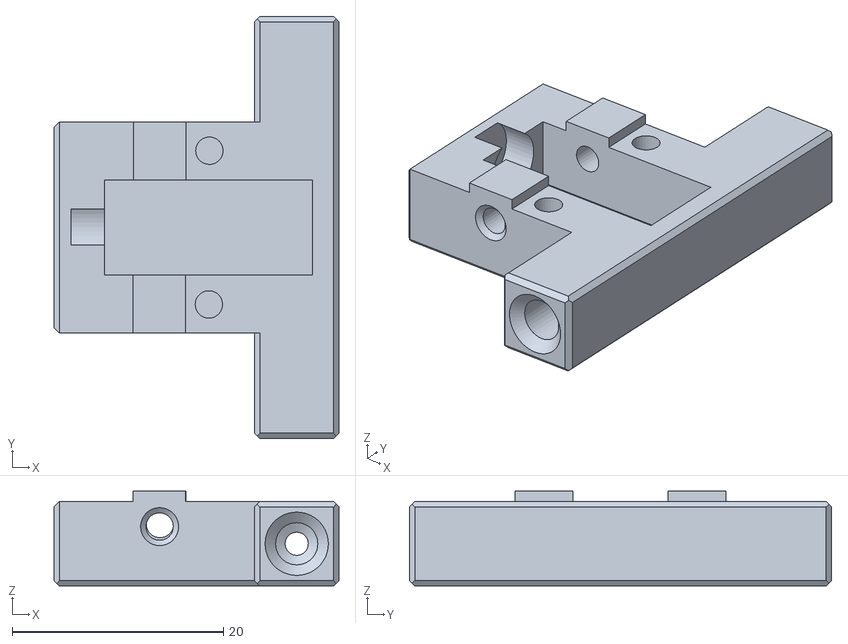
[picture p192: CAD file, 2022-07-15]
general/RunoutUnklicky/STLs/Base.stl
27.0 x 40.0 x 9.00
