MugenMicko/voron/V0/NozzleWiper/STLs/Carrier_Joint.stl

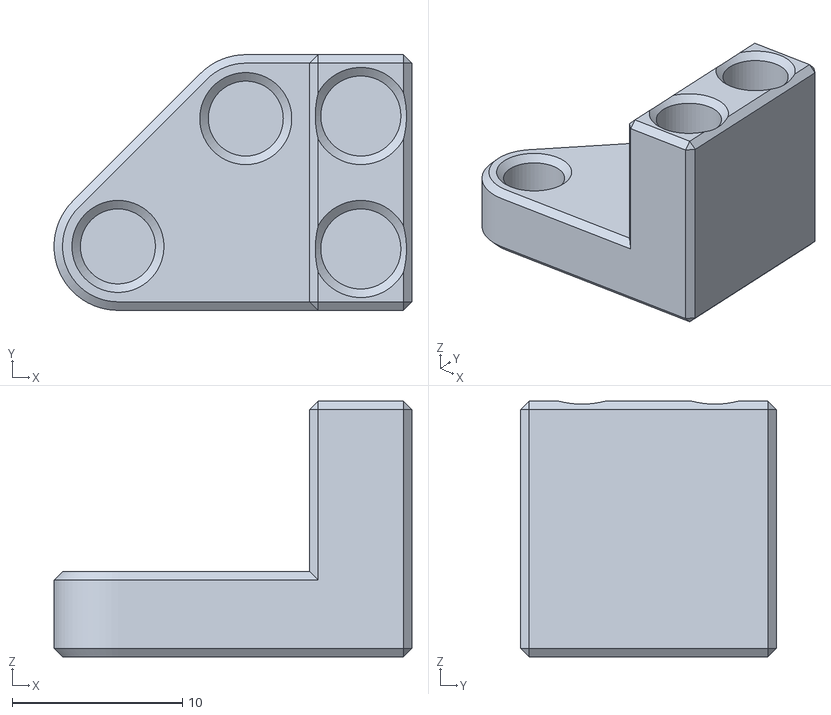
[picture p194: CAD file, 2022-08-21]
V0/NozzleWiper/STLs/Carrier_Joint.stl
21.0 x 15.0 x 15.0
