MugenMicko/voron/V0/Rapid_Burner/STLs/Cowl_SlideSwipe.stl

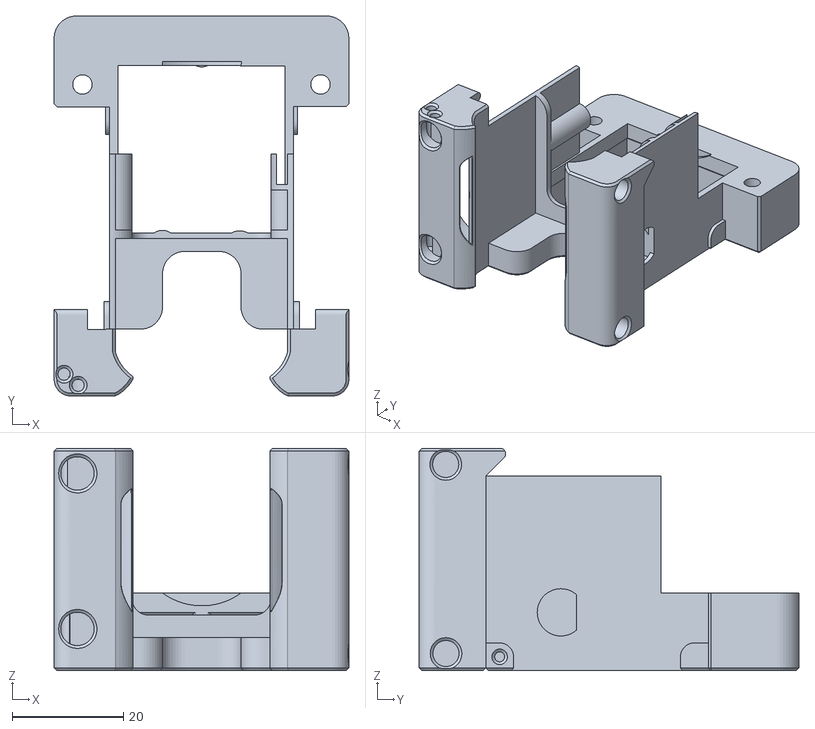
[picture p195: CAD file, 2022-09-04]
V0/Rapid_Burner/STLs/Cowl_SlideSwipe.stl
53.0 x 68.3 x 40.0
