MugenMicko/voron/V0/TipTophat/STLs/Mid_Door.stl

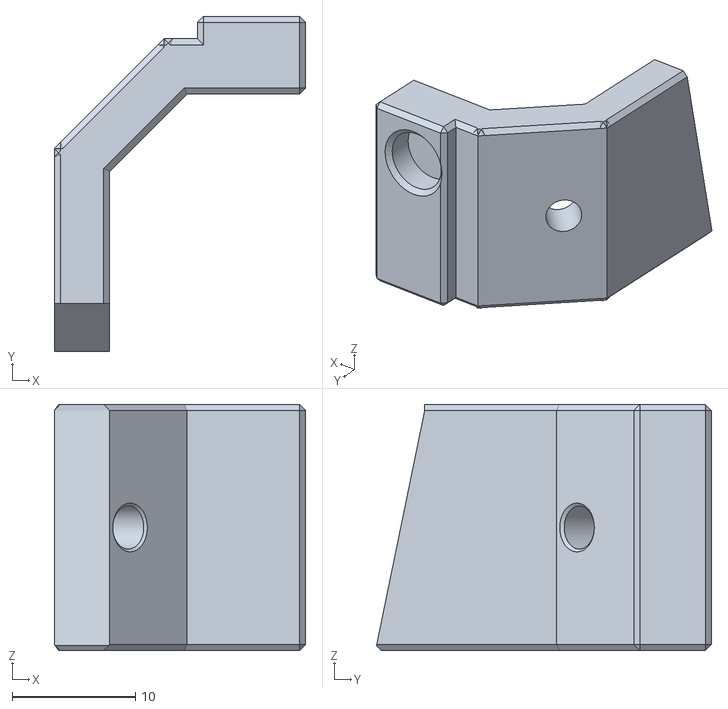
[picture p196: CAD file, 2022-06-30]
V0/TipTophat/STLs/Mid_Door.stl
20.4 x 27.2 x 20.0
