MugenMicko/voron/V0/TipTophat/STLs/Hinge_Right.stl

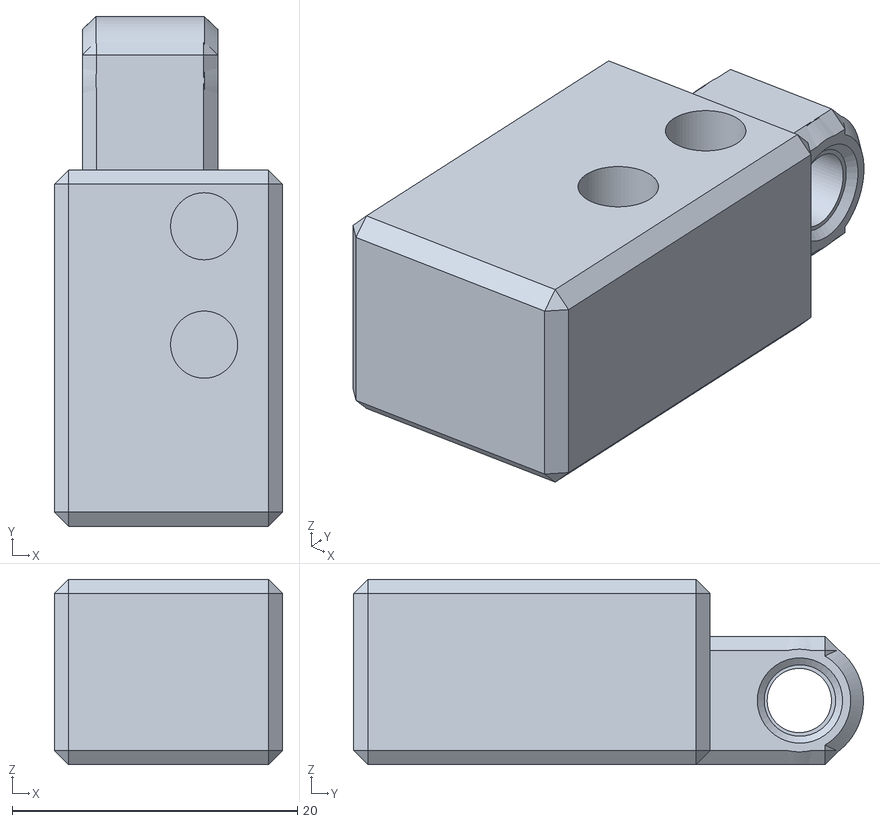
[picture p198: CAD file, 2022-06-30]
V0/TipTophat/STLs/Hinge_Right.stl
16.0 x 35.8 x 13.0
