MugenMicko/voron/V0/NozzleWiper/STLs/Brush_Carrier.stl

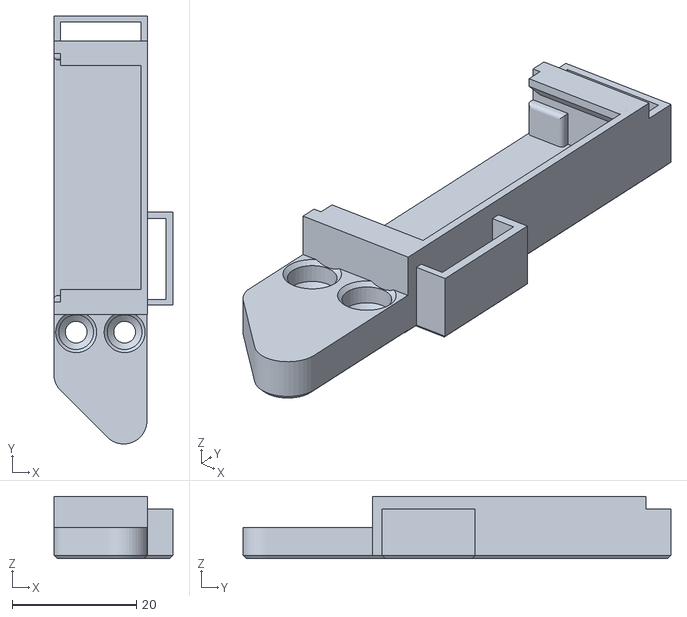
[picture p199: CAD file, 2022-07-25]
V0/NozzleWiper/STLs/Brush_Carrier.stl
19.1 x 68.9 x 10.0
