MugenMicko/voron/V0/Rapid_Burner/STLs/ADXL_Mount.stl

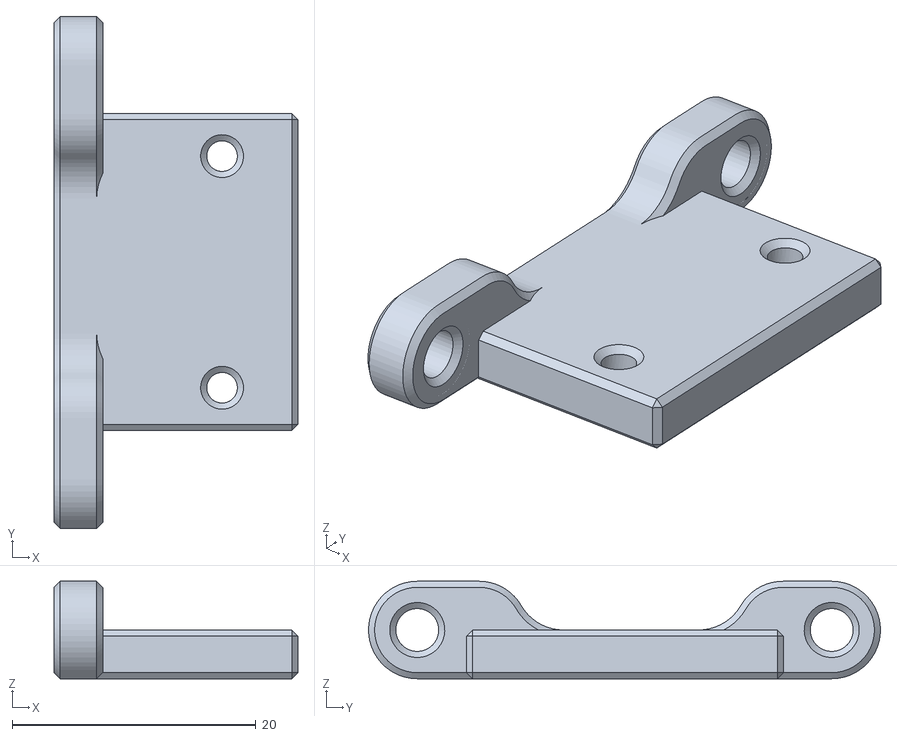
[picture p200: CAD file, 2022-08-26]
V0/Rapid_Burner/STLs/ADXL_Mount.stl
20.0 x 42.0 x 8.00
