MugenMicko/voron/V0/TipTophat/STLs/Door_Handle.stl

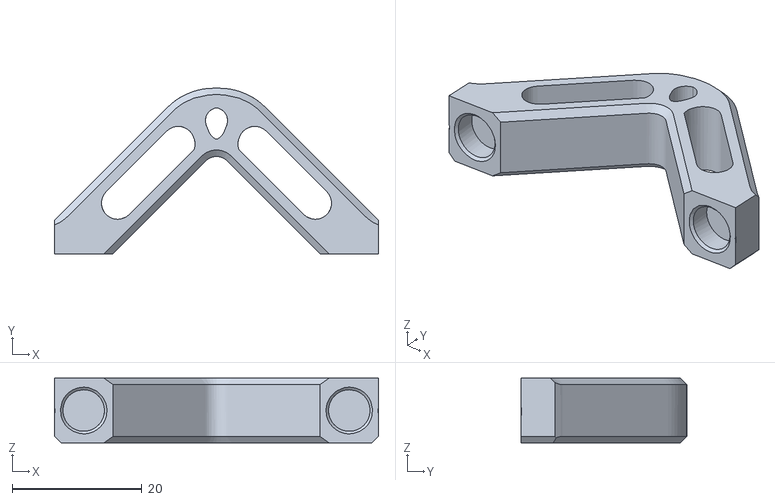
[picture p201: CAD file, 2022-06-30]
V0/TipTophat/STLs/Door_Handle.stl
49.9 x 25.5 x 10.0
