MugenMicko/voron/V0/5015_Toolhead/STLs/RevoVoron_Mount.stl

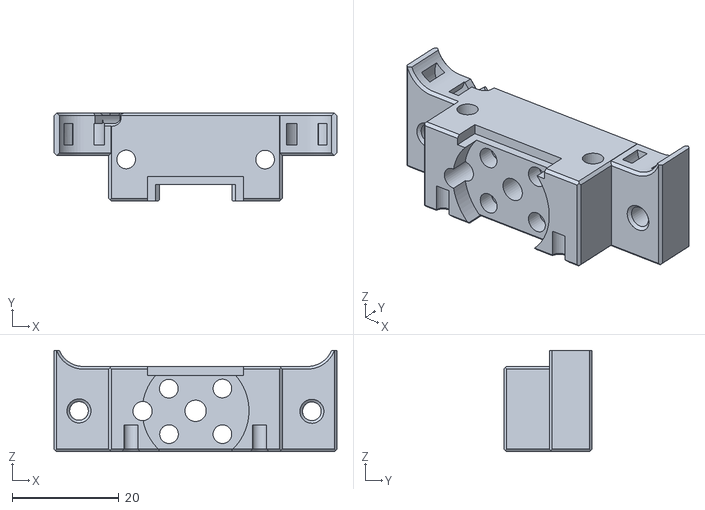
[picture p202: CAD file, 2022-08-30]
V0/5015_Toolhead/STLs/RevoVoron_Mount.stl
53.0 x 16.5 x 19.0
