MugenMicko/voron/V0/NozzleWiper/STLs/Allinone.stl

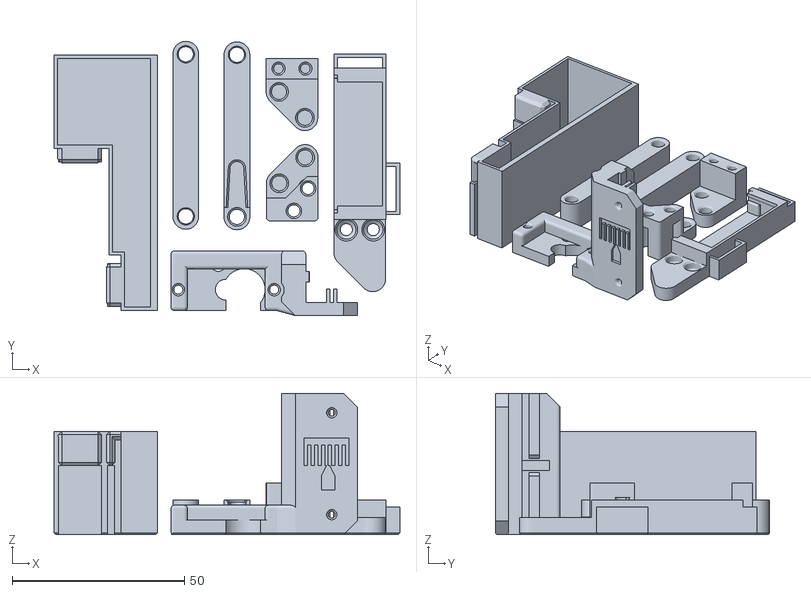
[picture p203: CAD file, 2022-07-25]
V0/NozzleWiper/STLs/Allinone.stl
100.3 x 79.6 x 41.0
