MugenMicko/voron/V0/TipTophat/STLs/Door_Frame.stl

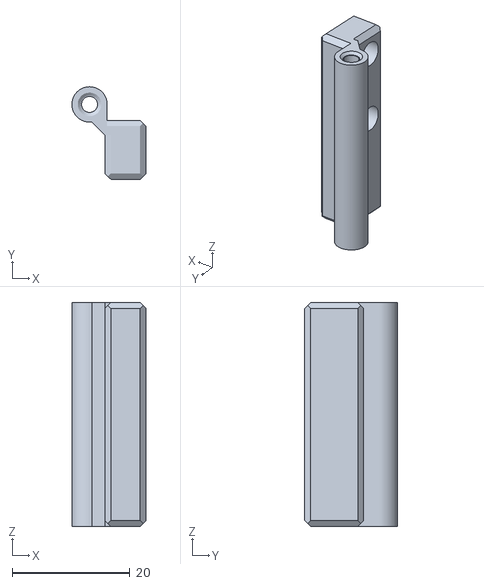
[picture p204: CAD file, 2022-06-30]
V0/TipTophat/STLs/Door_Frame.stl
12.6 x 15.7 x 38.0
