MugenMicko/voron/V0/NozzleWiper/STLs/Purge_Bucket.stl

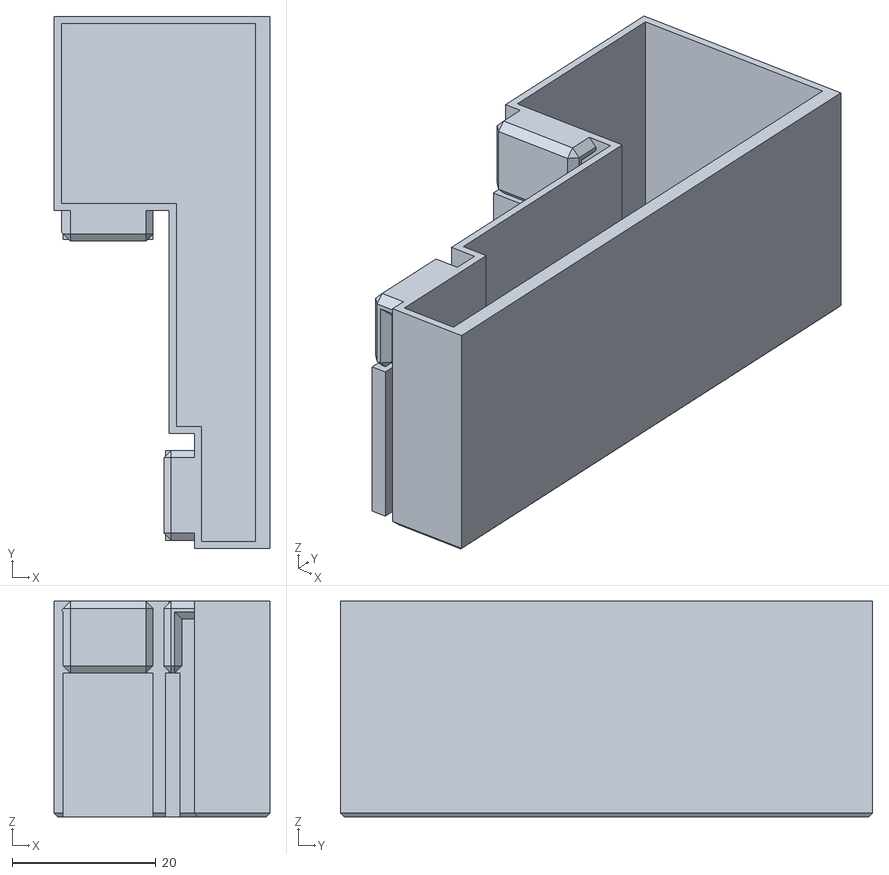
[picture p205: CAD file, 2022-07-25]
V0/NozzleWiper/STLs/Purge_Bucket.stl
30.0 x 74.0 x 30.0
