MugenMicko/voron/V0/TipTophat/STLs/Mid_Left_x2.stl

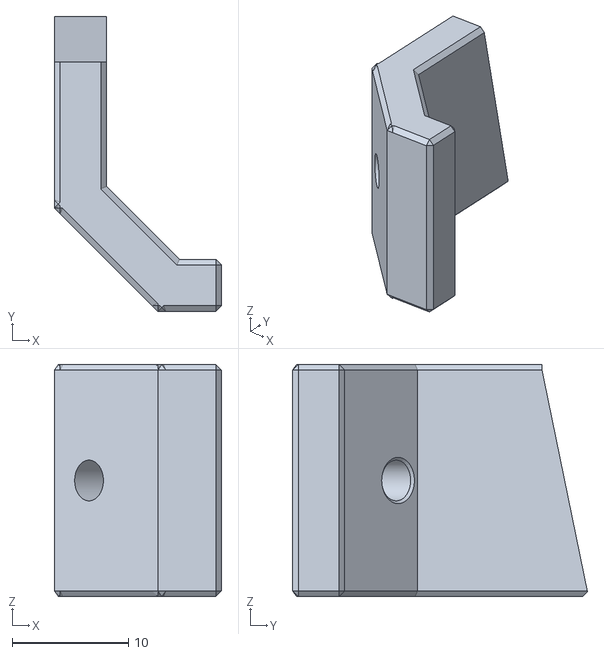
[picture p206: CAD file, 2022-06-30]
V0/TipTophat/STLs/Mid_Left_x2.stl
14.4 x 25.4 x 20.0
