MugenMicko/voron/V0/TipTophat/STLs/Body_Top_Center_x2.stl

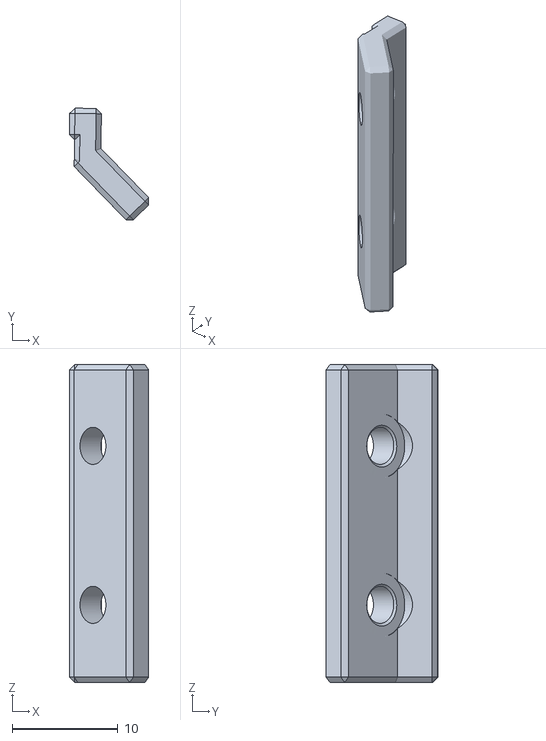
[picture p207: CAD file, 2022-06-30]
V0/TipTophat/STLs/Body_Top_Center_x2.stl
7.49 x 10.5 x 30.0
