MugenMicko/voron/V0/TipTophat/STLs/Top_Mid_x5.stl

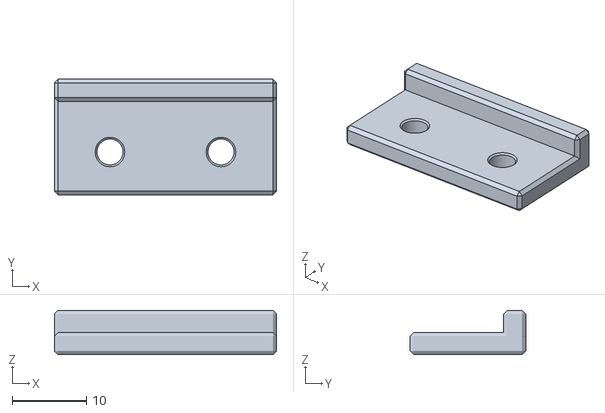
[picture p208: CAD file, 2022-06-30]
V0/TipTophat/STLs/Top_Mid_x5.stl
30.0 x 15.7 x 6.00
